Spectrewolf777/Stm32l4-Watch/Drivers/lvgl/lvgl/tests/ref_imgs/draw/render/al88/demo_render_image_normal_1_opa_128.png

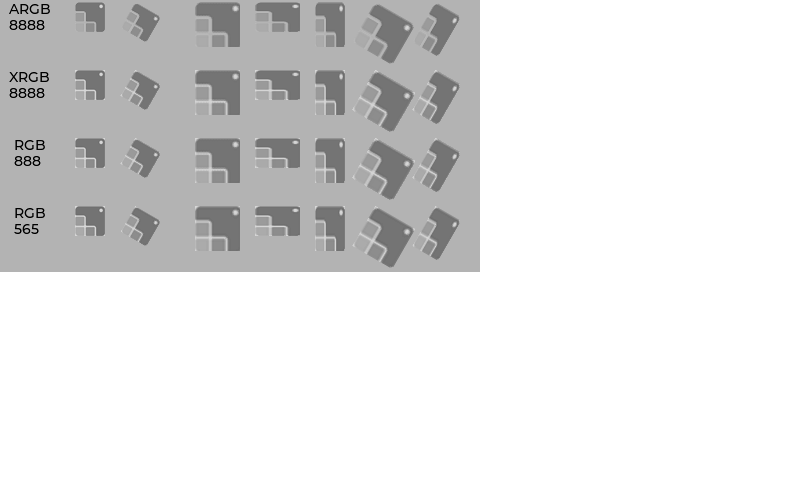
Drivers/lvgl/lvgl/tests/ref_imgs/draw/render/al88/demo_render_image_normal_1_opa_128.png
