Spectrewolf777/Stm32l4-Watch/Drivers/lvgl/lvgl/tests/ref_imgs/draw/render/argb8888/demo_render_arc_normal_opa_255.png

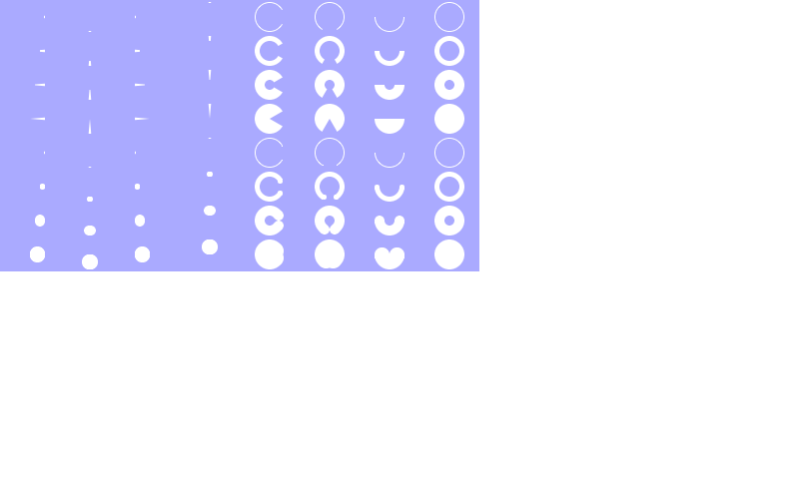
Drivers/lvgl/lvgl/tests/ref_imgs/draw/render/argb8888/demo_render_arc_normal_opa_255.png
