Spectrewolf777/Stm32l4-Watch/Drivers/lvgl/lvgl/tests/ref_imgs/draw/render/i1/demo_render_border_opa_192.png

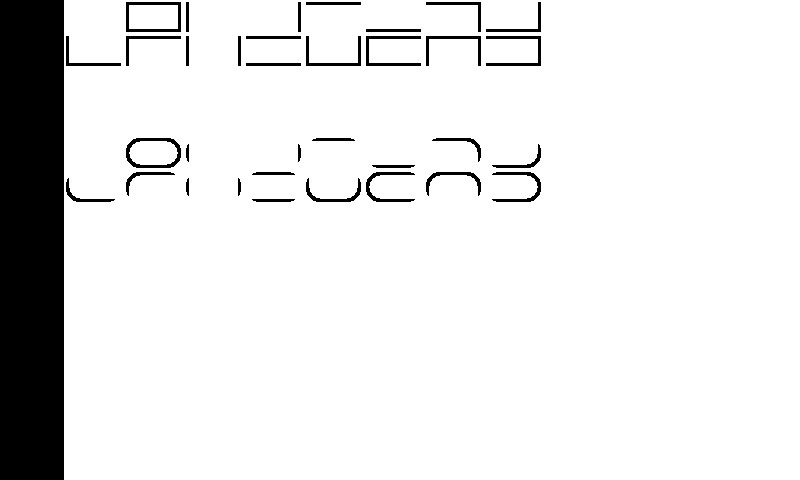
Drivers/lvgl/lvgl/tests/ref_imgs/draw/render/i1/demo_render_border_opa_192.png
