Spectrewolf777/Stm32l4-Watch/Drivers/lvgl/lvgl/tests/ref_imgs/draw/render/i1/demo_render_triangle_opa_255.png

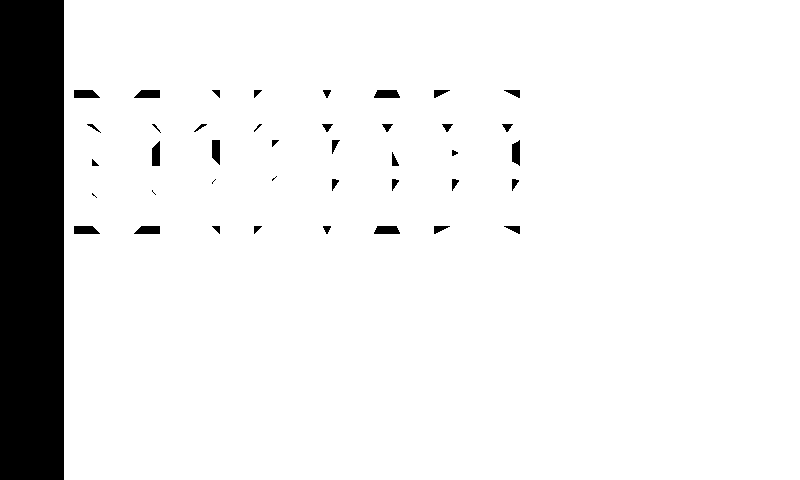
Drivers/lvgl/lvgl/tests/ref_imgs/draw/render/i1/demo_render_triangle_opa_255.png
