Spectrewolf777/Stm32l4-Watch/Drivers/lvgl/lvgl/tests/ref_imgs/draw/render/l8/demo_render_triangle_opa_128.png

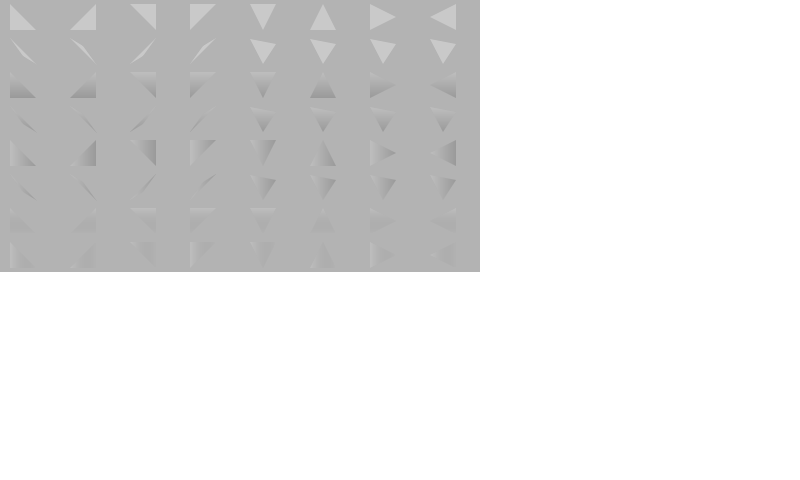
Drivers/lvgl/lvgl/tests/ref_imgs/draw/render/l8/demo_render_triangle_opa_128.png
