Spectrewolf777/Stm32l4-Watch/Drivers/lvgl/lvgl/tests/ref_imgs_vg_lite/draw/render/argb8888/demo_render_text_opa_128.png

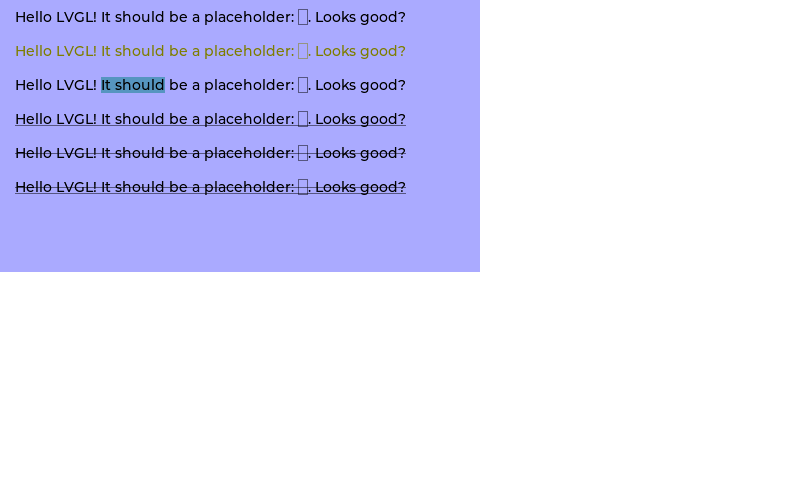
Drivers/lvgl/lvgl/tests/ref_imgs_vg_lite/draw/render/argb8888/demo_render_text_opa_128.png
