Spectrewolf777/Stm32l4-Watch/Core/Src/lsm6dsv16x_reg.c

/**
  ******************************************************************************
  * @file    lsm6dsv16x_reg.c
  * @author  Sensors Software Solution Team
  * @brief   LSM6DSV16X driver file
  ******************************************************************************
  * @attention
  *
  * Copyright (c) 2024 STMicroelectronics.
  * All rights reserved.
  *
  * This software is licensed under terms that can be found in the LICENSE file
  * in the root directory of this software component.
  * If no LICENSE file comes with this software, it is provided AS-IS.
  *
  ******************************************************************************
  */

#include <string.h>
#include "lsm6dsv16x_reg.h"

int32_t __weak lsm6dsv16x_read_reg(const stmdev_ctx_t *ctx, uint8_t reg,
                                   uint8_t *data,
                                   uint16_t len)
{
  int32_t ret = 0;

  if (ctx == NULL)
  {
    return -1;
  }

  ret = ctx->read_reg(ctx->handle, reg, data, len);

  return ret;
}

int32_t __weak lsm6dsv16x_write_reg(const stmdev_ctx_t *ctx, uint8_t reg,
                                    uint8_t *data,
                                    uint16_t len)
{
  int32_t ret = 0;

  if (ctx == NULL)
  {
    return -1;
  }

  ret = ctx->write_reg(ctx->handle, reg, data, len);

  return ret;
}

static void bytecpy(uint8_t *target, const uint8_t *source)
{
  if ((target != NULL) && (source != NULL))
  {
    *target = *source;
  }
}

float_t lsm6dsv16x_from_sflp_to_mg(int16_t lsb)
{
  return ((float_t)lsb) * 0.061f;
}

float_t lsm6dsv16x_from_fs2_to_mg(int16_t lsb)
{
  return ((float_t)lsb) * 0.061f;
}

float_t lsm6dsv16x_from_fs4_to_mg(int16_t lsb)
{
  return ((float_t)lsb) * 0.122f;
}

float_t lsm6dsv16x_from_fs8_to_mg(int16_t lsb)
{
  return ((float_t)lsb) * 0.244f;
}

float_t lsm6dsv16x_from_fs16_to_mg(int16_t lsb)
{
  return ((float_t)lsb) * 0.488f;
}

float_t lsm6dsv16x_from_fs125_to_mdps(int16_t lsb)
{
  return ((float_t)lsb) * 4.375f;
}

float_t lsm6dsv16x_from_fs250_to_mdps(int16_t lsb)
{
  return ((float_t)lsb) * 8.750f;
}

float_t lsm6dsv16x_from_fs500_to_mdps(int16_t lsb)
{
  return ((float_t)lsb) * 17.50f;
}

float_t lsm6dsv16x_from_fs1000_to_mdps(int16_t lsb)
{
  return ((float_t)lsb) * 35.0f;
}

float_t lsm6dsv16x_from_fs2000_to_mdps(int16_t lsb)
{
  return ((float_t)lsb) * 70.0f;
}

float_t lsm6dsv16x_from_fs4000_to_mdps(int16_t lsb)
{
  return ((float_t)lsb) * 140.0f;
}

float_t lsm6dsv16x_from_lsb_to_celsius(int16_t lsb)
{
  return (((float_t)lsb / 256.0f) + 25.0f);
}

float_t lsm6dsv16x_from_lsb_to_nsec(uint32_t lsb)
{
  return ((float_t)lsb * 21750.0f);
}

float_t lsm6dsv16x_from_lsb_to_mv(int16_t lsb)
{
  return ((float_t)lsb) / 78.0f;
}

/*
 * Original conversion routines taken from: https://github.com/numpy/numpy
 *
 * Converts from half-precision (16-bit) float number to single precision (32-bit).
 *
 * uint32_t  static uint32_t ToFloatBits(uint16_t h);
 * Released under BSD-3-Clause License
 */
static uint32_t ToFloatBits(uint16_t h)
{
  uint16_t h_exp = (h & 0x7c00u);
  uint32_t f_sgn = ((uint32_t)h & 0x8000u) << 16u;
  uint32_t result = {0};
  switch (h_exp)
  {
    case 0x0000u:   // 0 or subnormal
    {
      uint16_t h_sig = (h & 0x03ffu);
      // Signed zero
      if (h_sig == 0u)
      {
        result = f_sgn;
        break;
      }
      // Subnormal
      h_sig <<= 1u;
      while ((h_sig & 0x0400u) == 0u)
      {
        h_sig <<= 1u;
        h_exp++;
      }
      uint32_t f_exp = ((uint32_t)(127u - 15u - (uint32_t)h_exp)) << 23u;
      uint32_t f_sig = ((uint32_t)(h_sig & 0x03ffu)) << 13u;
      result = f_sgn + f_exp + f_sig;
      break;
    }
    case 0x7c00u: // inf or NaN
      // All-ones exponent and a copy of the significand
      result = f_sgn + 0x7f800000u + (((uint32_t)(h & 0x03ffu)) << 13u);
      break;
    default: // normalized
      // Just need to adjust the exponent and shift
      result = f_sgn + (((uint32_t)(h & 0x7fffu) + 0x1c000u) << 13u);
      break;
  }

  return result;
}

uint32_t lsm6dsv16x_from_f16_to_f32(uint16_t val)
{
  return ToFloatBits(val);
}


int32_t lsm6dsv16x_xl_offset_on_out_set(const stmdev_ctx_t *ctx, uint8_t val)
{
  lsm6dsv16x_ctrl9_t ctrl9 = {0};
  int32_t ret = 0;

  ret = lsm6dsv16x_read_reg(ctx, LSM6DSV16X_CTRL9, (uint8_t *)&ctrl9, 1);
  if (ret == 0)
  {
    ctrl9.usr_off_on_out = val;
    ret = lsm6dsv16x_write_reg(ctx, LSM6DSV16X_CTRL9, (uint8_t *)&ctrl9, 1);
  }

  return ret;
}

int32_t lsm6dsv16x_xl_offset_on_out_get(const stmdev_ctx_t *ctx, uint8_t *val)
{
  lsm6dsv16x_ctrl9_t ctrl9 = {0};
  int32_t ret = 0;

  ret = lsm6dsv16x_read_reg(ctx, LSM6DSV16X_CTRL9, (uint8_t *)&ctrl9, 1);
  if (ret != 0)
  {
    return ret;
  }

  *val = ctrl9.usr_off_on_out;

  return ret;
}

int32_t lsm6dsv16x_xl_offset_mg_set(const stmdev_ctx_t *ctx,
                                    lsm6dsv16x_xl_offset_mg_t val)
{
  lsm6dsv16x_z_ofs_usr_t z_ofs_usr = {0};
  lsm6dsv16x_y_ofs_usr_t y_ofs_usr = {0};
  lsm6dsv16x_x_ofs_usr_t x_ofs_usr = {0};
  lsm6dsv16x_ctrl9_t ctrl9 = {0};
  int32_t ret = 0;
  float_t tmp = 0;

  ret = lsm6dsv16x_read_reg(ctx, LSM6DSV16X_Z_OFS_USR, (uint8_t *)&z_ofs_usr, 1);
  ret += lsm6dsv16x_read_reg(ctx, LSM6DSV16X_Y_OFS_USR, (uint8_t *)&y_ofs_usr, 1);
  ret += lsm6dsv16x_read_reg(ctx, LSM6DSV16X_X_OFS_USR, (uint8_t *)&x_ofs_usr, 1);
  if (ret != 0)
  {
    return ret;
  }


  if ((val.x_mg < (0.0078125f * 127.0f)) && (val.x_mg > (0.0078125f * -127.0f)) &&
      (val.y_mg < (0.0078125f * 127.0f)) && (val.y_mg > (0.0078125f * -127.0f)) &&
      (val.z_mg < (0.0078125f * 127.0f)) && (val.z_mg > (0.0078125f * -127.0f)))
  {
    ctrl9.usr_off_w = 0;

    tmp = val.z_mg / 0.0078125f;
    z_ofs_usr.z_ofs_usr = (uint8_t)tmp;

    tmp = val.y_mg / 0.0078125f;
    y_ofs_usr.y_ofs_usr = (uint8_t)tmp;

    tmp = val.x_mg / 0.0078125f;
    x_ofs_usr.x_ofs_usr = (uint8_t)tmp;
  }
  else if ((val.x_mg < (0.125f * 127.0f)) && (val.x_mg > (0.125f * -127.0f)) &&
           (val.y_mg < (0.125f * 127.0f)) && (val.y_mg > (0.125f * -127.0f)) &&
           (val.z_mg < (0.125f * 127.0f)) && (val.z_mg > (0.125f * -127.0f)))
  {
    ctrl9.usr_off_w = 1;

    tmp = val.z_mg / 0.125f;
    z_ofs_usr.z_ofs_usr = (uint8_t)tmp;

    tmp = val.y_mg / 0.125f;
    y_ofs_usr.y_ofs_usr = (uint8_t)tmp;

    tmp = val.x_mg / 0.125f;
    x_ofs_usr.x_ofs_usr = (uint8_t)tmp;
  }
  else // out of limit
  {
    ctrl9.usr_off_w = 1;
    z_ofs_usr.z_ofs_usr = 0xFFU;
    y_ofs_usr.y_ofs_usr = 0xFFU;
    x_ofs_usr.x_ofs_usr = 0xFFU;
  }

  ret = lsm6dsv16x_write_reg(ctx, LSM6DSV16X_Z_OFS_USR, (uint8_t *)&z_ofs_usr, 1);
  ret += lsm6dsv16x_write_reg(ctx, LSM6DSV16X_Y_OFS_USR, (uint8_t *)&y_ofs_usr, 1);
  ret += lsm6dsv16x_write_reg(ctx, LSM6DSV16X_X_OFS_USR, (uint8_t *)&x_ofs_usr, 1);
  ret += lsm6dsv16x_write_reg(ctx, LSM6DSV16X_CTRL9, (uint8_t *)&ctrl9, 1);

  return ret;
}

int32_t lsm6dsv16x_xl_offset_mg_get(const stmdev_ctx_t *ctx,
                                    lsm6dsv16x_xl_offset_mg_t *val)
{
  lsm6dsv16x_z_ofs_usr_t z_ofs_usr = {0};
  lsm6dsv16x_y_ofs_usr_t y_ofs_usr = {0};
  lsm6dsv16x_x_ofs_usr_t x_ofs_usr = {0};
  lsm6dsv16x_ctrl9_t ctrl9 = {0};
  int32_t ret = 0;

  ret = lsm6dsv16x_read_reg(ctx, LSM6DSV16X_CTRL9, (uint8_t *)&ctrl9, 1);
  ret += lsm6dsv16x_read_reg(ctx, LSM6DSV16X_Z_OFS_USR, (uint8_t *)&z_ofs_usr, 1);
  ret += lsm6dsv16x_read_reg(ctx, LSM6DSV16X_Y_OFS_USR, (uint8_t *)&y_ofs_usr, 1);
  ret += lsm6dsv16x_read_reg(ctx, LSM6DSV16X_X_OFS_USR, (uint8_t *)&x_ofs_usr, 1);
  if (ret != 0)
  {
    return ret;
  }

  if (ctrl9.usr_off_w == PROPERTY_DISABLE)
  {
    val->z_mg = ((float_t)z_ofs_usr.z_ofs_usr * 0.0078125f);
    val->y_mg = ((float_t)y_ofs_usr.y_ofs_usr * 0.0078125f);
    val->x_mg = ((float_t)x_ofs_usr.x_ofs_usr * 0.0078125f);
  }
  else
  {
    val->z_mg = ((float_t)z_ofs_usr.z_ofs_usr * 0.125f);
    val->y_mg = ((float_t)y_ofs_usr.y_ofs_usr * 0.125f);
    val->x_mg = ((float_t)x_ofs_usr.x_ofs_usr * 0.125f);
  }

  return ret;
}

int32_t lsm6dsv16x_reboot(const stmdev_ctx_t *ctx)
{
  lsm6dsv16x_ctrl3_t ctrl3 = {0};
  lsm6dsv16x_data_rate_t data_rate_xl = {0};
  lsm6dsv16x_data_rate_t data_rate_gy = {0};
  int32_t ret = 0;

  if (ctx->mdelay == NULL)
  {
    ret = -1;
    goto exit;
  }

  ret = lsm6dsv16x_read_reg(ctx, LSM6DSV16X_CTRL3, (uint8_t *)&ctrl3, 1);
  if (ret != 0)
  {
    goto exit;
  }

  /* Save current data rates */
  ret = lsm6dsv16x_xl_data_rate_get(ctx, &data_rate_xl);
  ret += lsm6dsv16x_gy_data_rate_get(ctx, &data_rate_gy);
  if (ret != 0)
  {
    goto exit;
  }

  /* 1. Set the accelerometer and gyroscope in power-down mode */
  ret = lsm6dsv16x_xl_data_rate_set(ctx, LSM6DSV16X_ODR_OFF);
  ret += lsm6dsv16x_gy_data_rate_set(ctx, LSM6DSV16X_ODR_OFF);
  if (ret != 0)
  {
    goto exit;
  }

  /* 2. Set the BOOT bit of the CTRL3 register to 1. */
  ctrl3.boot = 1;
  ret = lsm6dsv16x_write_reg(ctx, LSM6DSV16X_CTRL3, (uint8_t *)&ctrl3, 1);
  if (ret != 0)
  {
    goto exit;
  }

  /* 3. Wait 30 ms. */
  ctx->mdelay(30);

  /* Restore data rates */
  ret = lsm6dsv16x_xl_data_rate_set(ctx, data_rate_xl);
  ret += lsm6dsv16x_gy_data_rate_set(ctx, data_rate_gy);

exit:
  return ret;
}

int32_t lsm6dsv16x_sw_por(const stmdev_ctx_t *ctx)
{
  lsm6dsv16x_func_cfg_access_t func_cfg_access = {0};
  int32_t ret = 0;

  if (ctx->mdelay == NULL)
  {
    ret = -1;
    goto exit;
  }

  /* 1. Set the SW_POR bit of the FUNC_CFG_ACCESS register to 1. */
  func_cfg_access.sw_por = 1;
  ret = lsm6dsv16x_write_reg(ctx, LSM6DSV16X_FUNC_CFG_ACCESS, (uint8_t *)&func_cfg_access, 1);
  if (ret != 0)
  {
    goto exit;
  }

  /* 2. Wait 30 ms. */
  ctx->mdelay(30);

exit:
  return ret;
}

int32_t lsm6dsv16x_sw_reset(const stmdev_ctx_t *ctx)
{
  lsm6dsv16x_ctrl3_t ctrl3 = {0};
  uint8_t retry = 0;
  int32_t ret = 0;

  if (ctx->mdelay == NULL)
  {
    ret = -1;
    goto exit;
  }

  /* 1. Set the accelerometer and gyroscope in power-down mode */
  ret = lsm6dsv16x_xl_data_rate_set(ctx, LSM6DSV16X_ODR_OFF);
  ret += lsm6dsv16x_gy_data_rate_set(ctx, LSM6DSV16X_ODR_OFF);
  if (ret != 0)
  {
    goto exit;
  }

  /* 2. Set the SW_RESET bit of the CTRL3 register to 1. */
  ctrl3.sw_reset = 1u;
  ret = lsm6dsv16x_write_reg(ctx, LSM6DSV16X_CTRL3, (uint8_t *)&ctrl3, 1);

  /* 3. Poll the SW_RESET bit of the CTRL3 register until it returns to 0. */
  do
  {
    ret += lsm6dsv16x_read_reg(ctx, LSM6DSV16X_CTRL3, (uint8_t *)&ctrl3, 1);
    if (ret != 0)
    {
      goto exit;
    }

    ctx->mdelay(1);
  } while (ctrl3.sw_reset == 1u && retry++ < 3u);

  return (ctrl3.sw_reset == 0u) ? 0 : -1;

exit:
  return ret;
}

int32_t lsm6dsv16x_mem_bank_set(const stmdev_ctx_t *ctx, lsm6dsv16x_mem_bank_t val)
{
  lsm6dsv16x_func_cfg_access_t func_cfg_access = {0};
  int32_t ret = 0;

  ret = lsm6dsv16x_read_reg(ctx, LSM6DSV16X_FUNC_CFG_ACCESS, (uint8_t *)&func_cfg_access, 1);
  if (ret != 0)
  {
    return ret;
  }

  func_cfg_access.shub_reg_access = ((uint8_t)val & 0x02U) >> 1;
  func_cfg_access.emb_func_reg_access = (uint8_t)val & 0x01U;
  ret = lsm6dsv16x_write_reg(ctx, LSM6DSV16X_FUNC_CFG_ACCESS, (uint8_t *)&func_cfg_access, 1);

  return ret;
}


int32_t lsm6dsv16x_mem_bank_get(const stmdev_ctx_t *ctx, lsm6dsv16x_mem_bank_t *val)
{
  lsm6dsv16x_func_cfg_access_t func_cfg_access = {0};
  int32_t ret = 0;

  ret = lsm6dsv16x_read_reg(ctx, LSM6DSV16X_FUNC_CFG_ACCESS, (uint8_t *)&func_cfg_access, 1);
  if (ret != 0)
  {
    return ret;
  }

  switch ((func_cfg_access.shub_reg_access << 1) + func_cfg_access.emb_func_reg_access)
  {
    case 0x00:
      *val = LSM6DSV16X_MAIN_MEM_BANK;
      break;

    case 0x01:
      *val = LSM6DSV16X_EMBED_FUNC_MEM_BANK;
      break;

    case 0x02:
      *val = LSM6DSV16X_SENSOR_HUB_MEM_BANK;
      break;

    default:
      *val = LSM6DSV16X_MAIN_MEM_BANK;
      break;
  }

  return ret;
}


int32_t lsm6dsv16x_device_id_get(const stmdev_ctx_t *ctx, uint8_t *val)
{
  int32_t ret = 0;

  ret = lsm6dsv16x_read_reg(ctx, LSM6DSV16X_WHO_AM_I, val, 1);

  return ret;
}

int32_t lsm6dsv16x_xl_data_rate_set(const stmdev_ctx_t *ctx,
                                    lsm6dsv16x_data_rate_t val)
{
  lsm6dsv16x_ctrl1_t ctrl1 = {0};
  lsm6dsv16x_haodr_cfg_t haodr = {0};
  uint8_t sel = 0;
  int32_t ret = 0;

  ret = lsm6dsv16x_read_reg(ctx, LSM6DSV16X_CTRL1, (uint8_t *)&ctrl1, 1);
  if (ret != 0)
  {
    return ret;
  }

  ctrl1.odr_xl = (uint8_t)val & 0x0Fu;
  ret = lsm6dsv16x_write_reg(ctx, LSM6DSV16X_CTRL1, (uint8_t *)&ctrl1, 1);
  if (ret != 0)
  {
    return ret;
  }

  sel = ((uint8_t)val >> 4) & 0xFU;
  if (sel != 0U)
  {
    ret += lsm6dsv16x_read_reg(ctx, LSM6DSV16X_HAODR_CFG, (uint8_t *)&haodr, 1);
    if (ret != 0)
    {
      return ret;
    }

    haodr.haodr_sel = sel;
    ret += lsm6dsv16x_write_reg(ctx, LSM6DSV16X_HAODR_CFG, (uint8_t *)&haodr, 1);
  }

  return ret;
}


int32_t lsm6dsv16x_xl_data_rate_get(const stmdev_ctx_t *ctx,
                                    lsm6dsv16x_data_rate_t *val)
{
  lsm6dsv16x_ctrl1_t ctrl1 = {0};
  lsm6dsv16x_haodr_cfg_t haodr = {0};
  uint8_t sel = 0;
  int32_t ret = 0;

  ret = lsm6dsv16x_read_reg(ctx, LSM6DSV16X_CTRL1, (uint8_t *)&ctrl1, 1);
  ret += lsm6dsv16x_read_reg(ctx, LSM6DSV16X_HAODR_CFG, (uint8_t *)&haodr, 1);
  if (ret != 0)
  {
    return ret;
  }

  sel = haodr.haodr_sel;

  switch (ctrl1.odr_xl)
  {
    case 0x00:
      *val = LSM6DSV16X_ODR_OFF;
      break;

    case 0x01:
      *val = LSM6DSV16X_ODR_AT_1Hz875;
      break;

    case 0x02:
      *val = LSM6DSV16X_ODR_AT_7Hz5;
      break;

    case 0x03:
      switch (sel)
      {
        default: /* sel == 0 or any unexpected value */
          *val = LSM6DSV16X_ODR_AT_15Hz;
          break;
        case 1:
          *val = LSM6DSV16X_ODR_HA01_AT_15Hz625;
          break;
        case 2:
          *val = LSM6DSV16X_ODR_HA02_AT_12Hz5;
          break;
      }
      break;

    case 0x04:
      switch (sel)
      {
        default: /* sel == 0 or any unexpected value */
          *val = LSM6DSV16X_ODR_AT_30Hz;
          break;
        case 1:
          *val = LSM6DSV16X_ODR_HA01_AT_31Hz25;
          break;
        case 2:
          *val = LSM6DSV16X_ODR_HA02_AT_25Hz;
          break;
      }
      break;

    case 0x05:
      switch (sel)
      {
        default: /* sel == 0 or any unexpected value */
          *val = LSM6DSV16X_ODR_AT_60Hz;
          break;
        case 1:
          *val = LSM6DSV16X_ODR_HA01_AT_62Hz5;
          break;
        case 2:
          *val = LSM6DSV16X_ODR_HA02_AT_50Hz;
          break;
      }
      break;

    case 0x06:
      switch (sel)
      {
        default: /* sel == 0 or any unexpected value */
          *val = LSM6DSV16X_ODR_AT_120Hz;
          break;
        case 1:
          *val = LSM6DSV16X_ODR_HA01_AT_125Hz;
          break;
        case 2:
          *val = LSM6DSV16X_ODR_HA02_AT_100Hz;
          break;
      }
      break;

    case 0x07:
      switch (sel)
      {
        default: /* sel == 0 or any unexpected value */
          *val = LSM6DSV16X_ODR_AT_240Hz;
          break;
        case 1:
          *val = LSM6DSV16X_ODR_HA01_AT_250Hz;
          break;
        case 2:
          *val = LSM6DSV16X_ODR_HA02_AT_200Hz;
          break;
      }
      break;

    case 0x08:
      switch (sel)
      {
        default: /* sel == 0 or any unexpected value */
          *val = LSM6DSV16X_ODR_AT_480Hz;
          break;
        case 1:
          *val = LSM6DSV16X_ODR_HA01_AT_500Hz;
          break;
        case 2:
          *val = LSM6DSV16X_ODR_HA02_AT_400Hz;
          break;
      }
      break;

    case 0x09:
      switch (sel)
      {
        default: /* sel == 0 or any unexpected value */
          *val = LSM6DSV16X_ODR_AT_960Hz;
          break;
        case 1:
          *val = LSM6DSV16X_ODR_HA01_AT_1000Hz;
          break;
        case 2:
          *val = LSM6DSV16X_ODR_HA02_AT_800Hz;
          break;
      }
      break;

    case 0x0A:
      switch (sel)
      {
        default: /* sel == 0 or any unexpected value */
          *val = LSM6DSV16X_ODR_AT_1920Hz;
          break;
        case 1:
          *val = LSM6DSV16X_ODR_HA01_AT_2000Hz;
          break;
        case 2:
          *val = LSM6DSV16X_ODR_HA02_AT_1600Hz;
          break;
      }
      break;

    case 0x0B:
      switch (sel)
      {
        default: /* sel == 0 or any unexpected value */
          *val = LSM6DSV16X_ODR_AT_3840Hz;
          break;
        case 1:
          *val = LSM6DSV16X_ODR_HA01_AT_4000Hz;
          break;
        case 2:
          *val = LSM6DSV16X_ODR_HA02_AT_3200Hz;
          break;
      }
      break;

    case 0x0C:
      switch (sel)
      {
        default: /* sel == 0 or any unexpected value */
          *val = LSM6DSV16X_ODR_AT_7680Hz;
          break;
        case 1:
          *val = LSM6DSV16X_ODR_HA01_AT_8000Hz;
          break;
        case 2:
          *val = LSM6DSV16X_ODR_HA02_AT_6400Hz;
          break;
      }
      break;

    default:
      *val = LSM6DSV16X_ODR_OFF;
      break;
  }

  return ret;
}


int32_t lsm6dsv16x_xl_mode_set(const stmdev_ctx_t *ctx, lsm6dsv16x_xl_mode_t val)
{
  lsm6dsv16x_ctrl1_t ctrl1 = {0};
  int32_t ret = 0;

  ret = lsm6dsv16x_read_reg(ctx, LSM6DSV16X_CTRL1, (uint8_t *)&ctrl1, 1);

  if (ret == 0)
  {
    ctrl1.op_mode_xl = (uint8_t)val & 0x07U;
    ret = lsm6dsv16x_write_reg(ctx, LSM6DSV16X_CTRL1, (uint8_t *)&ctrl1, 1);
  }

  return ret;
}

int32_t lsm6dsv16x_xl_mode_get(const stmdev_ctx_t *ctx, lsm6dsv16x_xl_mode_t *val)
{
  lsm6dsv16x_ctrl1_t ctrl1 = {0};
  int32_t ret = 0;

  ret = lsm6dsv16x_read_reg(ctx, LSM6DSV16X_CTRL1, (uint8_t *)&ctrl1, 1);
  if (ret != 0)
  {
    return ret;
  }

  switch (ctrl1.op_mode_xl)
  {
    case 0x00:
      *val = LSM6DSV16X_XL_HIGH_PERFORMANCE_MD;
      break;

    case 0x01:
      *val = LSM6DSV16X_XL_HIGH_ACCURACY_ODR_MD;
      break;

    case 0x03:
      *val = LSM6DSV16X_XL_ODR_TRIGGERED_MD;
      break;

    case 0x04:
      *val = LSM6DSV16X_XL_LOW_POWER_2_AVG_MD;
      break;

    case 0x05:
      *val = LSM6DSV16X_XL_LOW_POWER_4_AVG_MD;
      break;

    case 0x06:
      *val = LSM6DSV16X_XL_LOW_POWER_8_AVG_MD;
      break;

    case 0x07:
      *val = LSM6DSV16X_XL_NORMAL_MD;
      break;

    default:
      *val = LSM6DSV16X_XL_HIGH_PERFORMANCE_MD;
      break;
  }

  return ret;
}


int32_t lsm6dsv16x_gy_data_rate_set(const stmdev_ctx_t *ctx,
                                    lsm6dsv16x_data_rate_t val)
{
  lsm6dsv16x_ctrl2_t ctrl2 = {0};
  lsm6dsv16x_haodr_cfg_t haodr = {0};
  uint8_t sel = 0;
  int32_t ret = 0;

  ret = lsm6dsv16x_read_reg(ctx, LSM6DSV16X_CTRL2, (uint8_t *)&ctrl2, 1);
  if (ret != 0)
  {
    return ret;
  }

  ctrl2.odr_g = (uint8_t)val & 0x0Fu;
  ret += lsm6dsv16x_write_reg(ctx, LSM6DSV16X_CTRL2, (uint8_t *)&ctrl2, 1);
  if (ret != 0)
  {
    return ret;
  }

  sel = ((uint8_t)val >> 4) & 0xFU;
  if (sel != 0U)
  {
    ret += lsm6dsv16x_read_reg(ctx, LSM6DSV16X_HAODR_CFG, (uint8_t *)&haodr, 1);
    if (ret != 0)
    {
      return ret;
    }

    haodr.haodr_sel = sel;
    ret += lsm6dsv16x_write_reg(ctx, LSM6DSV16X_HAODR_CFG, (uint8_t *)&haodr, 1);
  }

  return ret;
}


int32_t lsm6dsv16x_gy_data_rate_get(const stmdev_ctx_t *ctx,
                                    lsm6dsv16x_data_rate_t *val)
{
  lsm6dsv16x_ctrl2_t ctrl2 = {0};
  lsm6dsv16x_haodr_cfg_t haodr = {0};
  uint8_t sel = 0;
  int32_t ret = 0;

  ret = lsm6dsv16x_read_reg(ctx, LSM6DSV16X_CTRL2, (uint8_t *)&ctrl2, 1);
  ret += lsm6dsv16x_read_reg(ctx, LSM6DSV16X_HAODR_CFG, (uint8_t *)&haodr, 1);
  if (ret != 0)
  {
    return ret;
  }

  sel = haodr.haodr_sel;

  switch (ctrl2.odr_g)
  {
    case 0x00:
      *val = LSM6DSV16X_ODR_OFF;
      break;

    case 0x01:
      *val = LSM6DSV16X_ODR_AT_1Hz875;
      break;

    case 0x02:
      *val = LSM6DSV16X_ODR_AT_7Hz5;
      break;

    case 0x03:
      switch (sel)
      {
        default: /* sel == 0 or any unexpected value */
          *val = LSM6DSV16X_ODR_AT_15Hz;
          break;
        case 1:
          *val = LSM6DSV16X_ODR_HA01_AT_15Hz625;
          break;
        case 2:
          *val = LSM6DSV16X_ODR_HA02_AT_12Hz5;
          break;
      }
      break;

    case 0x04:
      switch (sel)
      {
        default: /* sel == 0 or any unexpected value */
          *val = LSM6DSV16X_ODR_AT_30Hz;
          break;
        case 1:
          *val = LSM6DSV16X_ODR_HA01_AT_31Hz25;
          break;
        case 2:
          *val = LSM6DSV16X_ODR_HA02_AT_25Hz;
          break;
      }
      break;

    case 0x05:
      switch (sel)
      {
        default: /* sel == 0 or any unexpected value */
          *val = LSM6DSV16X_ODR_AT_60Hz;
          break;
        case 1:
          *val = LSM6DSV16X_ODR_HA01_AT_62Hz5;
          break;
        case 2:
          *val = LSM6DSV16X_ODR_HA02_AT_50Hz;
          break;
      }
      break;

    case 0x06:
      switch (sel)
      {
        default: /* sel == 0 or any unexpected value */
          *val = LSM6DSV16X_ODR_AT_120Hz;
          break;
        case 1:
          *val = LSM6DSV16X_ODR_HA01_AT_125Hz;
          break;
        case 2:
          *val = LSM6DSV16X_ODR_HA02_AT_100Hz;
          break;
      }
      break;

    case 0x07:
      switch (sel)
      {
        default: /* sel == 0 or any unexpected value */
          *val = LSM6DSV16X_ODR_AT_240Hz;
          break;
        case 1:
          *val = LSM6DSV16X_ODR_HA01_AT_250Hz;
          break;
        case 2:
          *val = LSM6DSV16X_ODR_HA02_AT_200Hz;
          break;
      }
      break;

    case 0x08:
      switch (sel)
      {
        default: /* sel == 0 or any unexpected value */
          *val = LSM6DSV16X_ODR_AT_480Hz;
          break;
        case 1:
          *val = LSM6DSV16X_ODR_HA01_AT_500Hz;
          break;
        case 2:
          *val = LSM6DSV16X_ODR_HA02_AT_400Hz;
          break;
      }
      break;

    case 0x09:
      switch (sel)
      {
        default: /* sel == 0 or any unexpected value */
          *val = LSM6DSV16X_ODR_AT_960Hz;
          break;
        case 1:
          *val = LSM6DSV16X_ODR_HA01_AT_1000Hz;
          break;
        case 2:
          *val = LSM6DSV16X_ODR_HA02_AT_800Hz;
          break;
      }
      break;

    case 0x0A:
      switch (sel)
      {
        default: /* sel == 0 or any unexpected value */
          *val = LSM6DSV16X_ODR_AT_1920Hz;
          break;
        case 1:
          *val = LSM6DSV16X_ODR_HA01_AT_2000Hz;
          break;
        case 2:
          *val = LSM6DSV16X_ODR_HA02_AT_1600Hz;
          break;
      }
      break;

    case 0x0B:
      switch (sel)
      {
        default: /* sel == 0 or any unexpected value */
          *val = LSM6DSV16X_ODR_AT_3840Hz;
          break;
        case 1:
          *val = LSM6DSV16X_ODR_HA01_AT_4000Hz;
          break;
        case 2:
          *val = LSM6DSV16X_ODR_HA02_AT_3200Hz;
          break;
      }
      break;

    case 0x0C:
      switch (sel)
      {
        default: /* sel == 0 or any unexpected value */
          *val = LSM6DSV16X_ODR_AT_7680Hz;
          break;
        case 1:
          *val = LSM6DSV16X_ODR_HA01_AT_8000Hz;
          break;
        case 2:
          *val = LSM6DSV16X_ODR_HA02_AT_6400Hz;
          break;
      }
      break;

    default:
      *val = LSM6DSV16X_ODR_OFF;
      break;
  }

  return ret;
}


int32_t lsm6dsv16x_gy_mode_set(const stmdev_ctx_t *ctx, lsm6dsv16x_gy_mode_t val)
{
  lsm6dsv16x_ctrl2_t ctrl2 = {0};
  int32_t ret = 0;

  ret = lsm6dsv16x_read_reg(ctx, LSM6DSV16X_CTRL2, (uint8_t *)&ctrl2, 1);
  if (ret == 0)
  {
    ctrl2.op_mode_g = (uint8_t)val & 0x07U;
    ret = lsm6dsv16x_write_reg(ctx, LSM6DSV16X_CTRL2, (uint8_t *)&ctrl2, 1);
  }

  return ret;
}


int32_t lsm6dsv16x_gy_mode_get(const stmdev_ctx_t *ctx, lsm6dsv16x_gy_mode_t *val)
{
  lsm6dsv16x_ctrl2_t ctrl2 = {0};
  int32_t ret = 0;

  ret = lsm6dsv16x_read_reg(ctx, LSM6DSV16X_CTRL2, (uint8_t *)&ctrl2, 1);
  if (ret != 0)
  {
    return ret;
  }

  switch (ctrl2.op_mode_g)
  {
    case 0x00:
      *val = LSM6DSV16X_GY_HIGH_PERFORMANCE_MD;
      break;

    case 0x01:
      *val = LSM6DSV16X_GY_HIGH_ACCURACY_ODR_MD;
      break;

    case 0x04:
      *val = LSM6DSV16X_GY_SLEEP_MD;
      break;

    case 0x05:
      *val = LSM6DSV16X_GY_LOW_POWER_MD;
      break;

    default:
      *val = LSM6DSV16X_GY_HIGH_PERFORMANCE_MD;
      break;
  }

  return ret;
}


int32_t lsm6dsv16x_auto_increment_set(const stmdev_ctx_t *ctx, uint8_t val)
{
  lsm6dsv16x_ctrl3_t ctrl3 = {0};
  int32_t ret = 0;

  ret = lsm6dsv16x_read_reg(ctx, LSM6DSV16X_CTRL3, (uint8_t *)&ctrl3, 1);
  if (ret == 0)
  {
    ctrl3.if_inc = val;
    ret = lsm6dsv16x_write_reg(ctx, LSM6DSV16X_CTRL3, (uint8_t *)&ctrl3, 1);
  }

  return ret;
}

int32_t lsm6dsv16x_auto_increment_get(const stmdev_ctx_t *ctx, uint8_t *val)
{
  lsm6dsv16x_ctrl3_t ctrl3 = {0};
  int32_t ret = 0;

  ret = lsm6dsv16x_read_reg(ctx, LSM6DSV16X_CTRL3, (uint8_t *)&ctrl3, 1);
  if (ret != 0)
  {
    return ret;
  }

  *val = ctrl3.if_inc;

  return ret;
}


int32_t lsm6dsv16x_block_data_update_set(const stmdev_ctx_t *ctx, uint8_t val)
{
  lsm6dsv16x_ctrl3_t ctrl3 = {0};
  int32_t ret = 0;

  ret = lsm6dsv16x_read_reg(ctx, LSM6DSV16X_CTRL3, (uint8_t *)&ctrl3, 1);

  if (ret == 0)
  {
    ctrl3.bdu = val;
    ret = lsm6dsv16x_write_reg(ctx, LSM6DSV16X_CTRL3, (uint8_t *)&ctrl3, 1);
  }

  return ret;
}

int32_t lsm6dsv16x_block_data_update_get(const stmdev_ctx_t *ctx, uint8_t *val)
{
  lsm6dsv16x_ctrl3_t ctrl3 = {0};
  int32_t ret = 0;

  ret = lsm6dsv16x_read_reg(ctx, LSM6DSV16X_CTRL3, (uint8_t *)&ctrl3, 1);
  if (ret != 0)
  {
    return ret;
  }

  *val = ctrl3.bdu;

  return ret;
}


int32_t lsm6dsv16x_odr_trig_cfg_set(const stmdev_ctx_t *ctx, uint8_t val)
{
  lsm6dsv16x_odr_trig_cfg_t odr_trig = {0};
  int32_t ret = 0;

  if (val >= 1U && val <= 3U)
  {
    return -1;
  }

  ret = lsm6dsv16x_read_reg(ctx, LSM6DSV16X_ODR_TRIG_CFG, (uint8_t *)&odr_trig, 1);

  if (ret == 0)
  {
    odr_trig.odr_trig_nodr = val;
    ret = lsm6dsv16x_write_reg(ctx, LSM6DSV16X_ODR_TRIG_CFG, (uint8_t *)&odr_trig, 1);
  }

  return ret;
}


int32_t lsm6dsv16x_odr_trig_cfg_get(const stmdev_ctx_t *ctx, uint8_t *val)
{
  lsm6dsv16x_odr_trig_cfg_t odr_trig = {0};
  int32_t ret = 0;

  ret = lsm6dsv16x_read_reg(ctx, LSM6DSV16X_ODR_TRIG_CFG, (uint8_t *)&odr_trig, 1);
  if (ret != 0)
  {
    return ret;
  }

  *val = odr_trig.odr_trig_nodr;

  return ret;
}


int32_t lsm6dsv16x_data_ready_mode_set(const stmdev_ctx_t *ctx,
                                       lsm6dsv16x_data_ready_mode_t val)
{
  lsm6dsv16x_ctrl4_t ctrl4 = {0};
  int32_t ret = 0;

  ret = lsm6dsv16x_read_reg(ctx, LSM6DSV16X_CTRL4, (uint8_t *)&ctrl4, 1);

  if (ret == 0)
  {
    ctrl4.drdy_pulsed = (uint8_t)val & 0x1U;
    ret = lsm6dsv16x_write_reg(ctx, LSM6DSV16X_CTRL4, (uint8_t *)&ctrl4, 1);
  }

  return ret;
}


int32_t lsm6dsv16x_data_ready_mode_get(const stmdev_ctx_t *ctx,
                                       lsm6dsv16x_data_ready_mode_t *val)
{
  lsm6dsv16x_ctrl4_t ctrl4 = {0};
  int32_t ret = 0;

  ret = lsm6dsv16x_read_reg(ctx, LSM6DSV16X_CTRL4, (uint8_t *)&ctrl4, 1);
  if (ret != 0)
  {
    return ret;
  }

  switch (ctrl4.drdy_pulsed)
  {
    case 0x00:
      *val = LSM6DSV16X_DRDY_LATCHED;
      break;

    case 0x01:
      *val = LSM6DSV16X_DRDY_PULSED;
      break;

    default:
      *val = LSM6DSV16X_DRDY_LATCHED;
      break;
  }

  return ret;
}


int32_t lsm6dsv16x_interrupt_enable_set(const stmdev_ctx_t *ctx,
                                        lsm6dsv16x_interrupt_mode_t val)
{
  lsm6dsv16x_tap_cfg0_t cfg = {0};
  lsm6dsv16x_functions_enable_t func = {0};
  int32_t ret = 0;

  ret = lsm6dsv16x_read_reg(ctx, LSM6DSV16X_FUNCTIONS_ENABLE, (uint8_t *)&func, 1);
  if (ret != 0)
  {
    return ret;
  }
  func.interrupts_enable = val.enable;
  ret = lsm6dsv16x_write_reg(ctx, LSM6DSV16X_FUNCTIONS_ENABLE, (uint8_t *)&func, 1);

  ret += lsm6dsv16x_read_reg(ctx, LSM6DSV16X_TAP_CFG0, (uint8_t *)&cfg, 1);
  if (ret != 0)
  {
    return ret;
  }
  cfg.lir = val.lir;
  ret += lsm6dsv16x_write_reg(ctx, LSM6DSV16X_TAP_CFG0, (uint8_t *)&cfg, 1);

  return ret;
}


int32_t lsm6dsv16x_interrupt_enable_get(const stmdev_ctx_t *ctx,
                                        lsm6dsv16x_interrupt_mode_t *val)
{
  lsm6dsv16x_tap_cfg0_t cfg = {0};
  lsm6dsv16x_functions_enable_t func = {0};
  int32_t ret = 0;

  ret = lsm6dsv16x_read_reg(ctx, LSM6DSV16X_FUNCTIONS_ENABLE, (uint8_t *)&func, 1);
  ret += lsm6dsv16x_read_reg(ctx, LSM6DSV16X_TAP_CFG0, (uint8_t *)&cfg, 1);
  if (ret != 0)
  {
    return ret;
  }

  val->enable = func.interrupts_enable;
  val->lir = cfg.lir;

  return ret;
}


int32_t lsm6dsv16x_gy_full_scale_set(const stmdev_ctx_t *ctx,
                                     lsm6dsv16x_gy_full_scale_t val)
{
  lsm6dsv16x_ctrl6_t ctrl6 = {0};
  int32_t ret = 0;

  ret = lsm6dsv16x_read_reg(ctx, LSM6DSV16X_CTRL6, (uint8_t *)&ctrl6, 1);

  if (ret == 0)
  {
    ctrl6.fs_g = (uint8_t)val & 0xfu;
    ret = lsm6dsv16x_write_reg(ctx, LSM6DSV16X_CTRL6, (uint8_t *)&ctrl6, 1);
  }

  return ret;
}


int32_t lsm6dsv16x_gy_full_scale_get(const stmdev_ctx_t *ctx,
                                     lsm6dsv16x_gy_full_scale_t *val)
{
  lsm6dsv16x_ctrl6_t ctrl6 = {0};
  int32_t ret = 0;

  ret = lsm6dsv16x_read_reg(ctx, LSM6DSV16X_CTRL6, (uint8_t *)&ctrl6, 1);
  if (ret != 0)
  {
    return ret;
  }

  switch (ctrl6.fs_g)
  {
    case 0x00:
      *val = LSM6DSV16X_125dps;
      break;

    case 0x01:
      *val = LSM6DSV16X_250dps;
      break;

    case 0x02:
      *val = LSM6DSV16X_500dps;
      break;

    case 0x03:
      *val = LSM6DSV16X_1000dps;
      break;

    case 0x04:
      *val = LSM6DSV16X_2000dps;
      break;

    case 0x0C:
      *val = LSM6DSV16X_4000dps;
      break;

    default:
      *val = LSM6DSV16X_125dps;
      break;
  }

  return ret;
}


int32_t lsm6dsv16x_xl_full_scale_set(const stmdev_ctx_t *ctx,
                                     lsm6dsv16x_xl_full_scale_t val)
{
  lsm6dsv16x_ctrl8_t ctrl8 = {0};
  int32_t ret = 0;

  ret = lsm6dsv16x_read_reg(ctx, LSM6DSV16X_CTRL8, (uint8_t *)&ctrl8, 1);

  if (ret == 0)
  {
    ctrl8.fs_xl = (uint8_t)val & 0x3U;
    ret = lsm6dsv16x_write_reg(ctx, LSM6DSV16X_CTRL8, (uint8_t *)&ctrl8, 1);
  }

  return ret;
}


int32_t lsm6dsv16x_xl_full_scale_get(const stmdev_ctx_t *ctx,
                                     lsm6dsv16x_xl_full_scale_t *val)
{
  lsm6dsv16x_ctrl8_t ctrl8 = {0};
  int32_t ret = 0;

  ret = lsm6dsv16x_read_reg(ctx, LSM6DSV16X_CTRL8, (uint8_t *)&ctrl8, 1);
  if (ret != 0)
  {
    return ret;
  }

  switch (ctrl8.fs_xl)
  {
    case 0x00:
      *val = LSM6DSV16X_2g;
      break;

    case 0x01:
      *val = LSM6DSV16X_4g;
      break;

    case 0x02:
      *val = LSM6DSV16X_8g;
      break;

    case 0x03:
      *val = LSM6DSV16X_16g;
      break;

    default:
      *val = LSM6DSV16X_2g;
      break;
  }

  return ret;
}


int32_t lsm6dsv16x_xl_dual_channel_set(const stmdev_ctx_t *ctx, uint8_t val)
{
  lsm6dsv16x_ctrl8_t ctrl8 = {0};
  int32_t ret = 0;

  ret = lsm6dsv16x_read_reg(ctx, LSM6DSV16X_CTRL8, (uint8_t *)&ctrl8, 1);

  if (ret == 0)
  {
    ctrl8.xl_dualc_en = val;
    ret = lsm6dsv16x_write_reg(ctx, LSM6DSV16X_CTRL8, (uint8_t *)&ctrl8, 1);
  }

  return ret;
}

int32_t lsm6dsv16x_xl_dual_channel_get(const stmdev_ctx_t *ctx, uint8_t *val)
{
  lsm6dsv16x_ctrl8_t ctrl8 = {0};
  int32_t ret = 0;

  ret = lsm6dsv16x_read_reg(ctx, LSM6DSV16X_CTRL8, (uint8_t *)&ctrl8, 1);
  if (ret != 0)
  {
    return ret;
  }

  *val = ctrl8.xl_dualc_en;

  return ret;
}


int32_t lsm6dsv16x_xl_self_test_set(const stmdev_ctx_t *ctx,
                                    lsm6dsv16x_xl_self_test_t val)
{
  lsm6dsv16x_ctrl10_t ctrl10 = {0};
  int32_t ret = 0;

  ret = lsm6dsv16x_read_reg(ctx, LSM6DSV16X_CTRL10, (uint8_t *)&ctrl10, 1);

  if (ret == 0)
  {
    ctrl10.st_xl = (uint8_t)val & 0x3U;
    ret = lsm6dsv16x_write_reg(ctx, LSM6DSV16X_CTRL10, (uint8_t *)&ctrl10, 1);
  }

  return ret;
}


int32_t lsm6dsv16x_xl_self_test_get(const stmdev_ctx_t *ctx,
                                    lsm6dsv16x_xl_self_test_t *val)
{
  lsm6dsv16x_ctrl10_t ctrl10 = {0};
  int32_t ret = 0;

  ret = lsm6dsv16x_read_reg(ctx, LSM6DSV16X_CTRL10, (uint8_t *)&ctrl10, 1);
  if (ret != 0)
  {
    return ret;
  }

  switch (ctrl10.st_xl)
  {
    case 0x00:
      *val = LSM6DSV16X_XL_ST_DISABLE;
      break;

    case 0x01:
      *val = LSM6DSV16X_XL_ST_POSITIVE;
      break;

    case 0x02:
      *val = LSM6DSV16X_XL_ST_NEGATIVE;
      break;

    default:
      *val = LSM6DSV16X_XL_ST_DISABLE;
      break;
  }

  return ret;
}


int32_t lsm6dsv16x_gy_self_test_set(const stmdev_ctx_t *ctx,
                                    lsm6dsv16x_gy_self_test_t val)
{
  lsm6dsv16x_ctrl10_t ctrl10 = {0};
  int32_t ret = 0;

  ret = lsm6dsv16x_read_reg(ctx, LSM6DSV16X_CTRL10, (uint8_t *)&ctrl10, 1);

  if (ret == 0)
  {
    ctrl10.st_g = (uint8_t)val & 0x3U;
    ret = lsm6dsv16x_write_reg(ctx, LSM6DSV16X_CTRL10, (uint8_t *)&ctrl10, 1);
  }

  return ret;
}


int32_t lsm6dsv16x_gy_self_test_get(const stmdev_ctx_t *ctx,
                                    lsm6dsv16x_gy_self_test_t *val)
{
  lsm6dsv16x_ctrl10_t ctrl10 = {0};
  int32_t ret = 0;

  ret = lsm6dsv16x_read_reg(ctx, LSM6DSV16X_CTRL10, (uint8_t *)&ctrl10, 1);
  if (ret != 0)
  {
    return ret;
  }

  switch (ctrl10.st_g)
  {
    case 0x00:
      *val = LSM6DSV16X_GY_ST_DISABLE;
      break;

    case 0x01:
      *val = LSM6DSV16X_GY_ST_POSITIVE;
      break;

    case 0x02:
      *val = LSM6DSV16X_GY_ST_NEGATIVE;
      break;

    default:
      *val = LSM6DSV16X_GY_ST_DISABLE;
      break;
  }

  return ret;
}


int32_t lsm6dsv16x_ois_xl_self_test_set(const stmdev_ctx_t *ctx,
                                        lsm6dsv16x_ois_xl_self_test_t val)
{
  lsm6dsv16x_spi2_int_ois_t spi2_int_ois = {0};
  int32_t ret = 0;

  ret = lsm6dsv16x_read_reg(ctx, LSM6DSV16X_SPI2_INT_OIS, (uint8_t *)&spi2_int_ois, 1);

  if (ret == 0)
  {
    spi2_int_ois.st_xl_ois = ((uint8_t)val & 0x3U);
    ret = lsm6dsv16x_write_reg(ctx, LSM6DSV16X_SPI2_INT_OIS, (uint8_t *)&spi2_int_ois, 1);
  }

  return ret;
}


int32_t lsm6dsv16x_ois_xl_self_test_get(const stmdev_ctx_t *ctx,
                                        lsm6dsv16x_ois_xl_self_test_t *val)
{
  lsm6dsv16x_spi2_int_ois_t spi2_int_ois = {0};
  int32_t ret = 0;

  ret = lsm6dsv16x_read_reg(ctx, LSM6DSV16X_SPI2_INT_OIS, (uint8_t *)&spi2_int_ois, 1);
  if (ret != 0)
  {
    return ret;
  }

  switch (spi2_int_ois.st_xl_ois)
  {
    case 0x00:
      *val = LSM6DSV16X_OIS_XL_ST_DISABLE;
      break;

    case 0x01:
      *val = LSM6DSV16X_OIS_XL_ST_POSITIVE;
      break;

    case 0x02:
      *val = LSM6DSV16X_OIS_XL_ST_NEGATIVE;
      break;

    default:
      *val = LSM6DSV16X_OIS_XL_ST_DISABLE;
      break;
  }

  return ret;
}


int32_t lsm6dsv16x_ois_gy_self_test_set(const stmdev_ctx_t *ctx,
                                        lsm6dsv16x_ois_gy_self_test_t val)
{
  lsm6dsv16x_spi2_int_ois_t spi2_int_ois = {0};
  int32_t ret = 0;

  ret = lsm6dsv16x_read_reg(ctx, LSM6DSV16X_SPI2_INT_OIS, (uint8_t *)&spi2_int_ois, 1);

  if (ret == 0)
  {
    spi2_int_ois.st_g_ois = ((uint8_t)val & 0x3U);
    spi2_int_ois.st_ois_clampdis = ((uint8_t)val & 0x04U) >> 2;
    ret = lsm6dsv16x_write_reg(ctx, LSM6DSV16X_SPI2_INT_OIS, (uint8_t *)&spi2_int_ois, 1);
  }

  return ret;
}


int32_t lsm6dsv16x_ois_gy_self_test_get(const stmdev_ctx_t *ctx,
                                        lsm6dsv16x_ois_gy_self_test_t *val)
{
  lsm6dsv16x_spi2_int_ois_t spi2_int_ois = {0};
  int32_t ret = 0;

  ret = lsm6dsv16x_read_reg(ctx, LSM6DSV16X_SPI2_INT_OIS, (uint8_t *)&spi2_int_ois, 1);
  if (ret != 0)
  {
    return ret;
  }

  switch (spi2_int_ois.st_g_ois)
  {
    case 0x00:
      *val = LSM6DSV16X_OIS_GY_ST_DISABLE;
      break;

    case 0x01:
      *val = (spi2_int_ois.st_ois_clampdis == 1U) ? LSM6DSV16X_OIS_GY_ST_CLAMP_POS :
             LSM6DSV16X_OIS_GY_ST_POSITIVE;
      break;

    case 0x02:
      *val = (spi2_int_ois.st_ois_clampdis == 1U) ? LSM6DSV16X_OIS_GY_ST_CLAMP_NEG :
             LSM6DSV16X_OIS_GY_ST_NEGATIVE;
      break;

    default:
      *val = LSM6DSV16X_OIS_GY_ST_DISABLE;
      break;
  }

  return ret;
}

int32_t lsm6dsv16x_pin_int1_route_set(const stmdev_ctx_t *ctx,
                                      lsm6dsv16x_pin_int_route_t *val)
{
  lsm6dsv16x_int1_ctrl_t          int1_ctrl = {0};
  lsm6dsv16x_md1_cfg_t            md1_cfg = {0};
  int32_t                    ret = 0;

  ret = lsm6dsv16x_read_reg(ctx, LSM6DSV16X_INT1_CTRL, (uint8_t *)&int1_ctrl, 1);
  if (ret != 0)
  {
    return ret;
  }

  int1_ctrl.int1_drdy_xl       = val->drdy_xl;
  int1_ctrl.int1_drdy_g        = val->drdy_g;
  int1_ctrl.int1_fifo_th       = val->fifo_th;
  int1_ctrl.int1_fifo_ovr      = val->fifo_ovr;
  int1_ctrl.int1_fifo_full     = val->fifo_full;
  int1_ctrl.int1_cnt_bdr       = val->cnt_bdr;

  ret = lsm6dsv16x_write_reg(ctx, LSM6DSV16X_INT1_CTRL, (uint8_t *)&int1_ctrl, 1);

  ret += lsm6dsv16x_read_reg(ctx, LSM6DSV16X_MD1_CFG, (uint8_t *)&md1_cfg, 1);
  if (ret != 0)
  {
    return ret;
  }

  md1_cfg.int1_shub            = val->shub;
  md1_cfg.int1_emb_func        = val->emb_func;
  md1_cfg.int1_6d              = val->sixd;
  md1_cfg.int1_single_tap      = val->single_tap;
  md1_cfg.int1_double_tap      = val->double_tap;
  md1_cfg.int1_wu              = val->wakeup;
  md1_cfg.int1_ff              = val->freefall;
  md1_cfg.int1_sleep_change    = val->sleep_change;

  ret = lsm6dsv16x_write_reg(ctx, LSM6DSV16X_MD1_CFG, (uint8_t *)&md1_cfg, 1);

  return ret;
}


int32_t lsm6dsv16x_pin_int1_route_get(const stmdev_ctx_t *ctx,
                                      lsm6dsv16x_pin_int_route_t *val)
{
  lsm6dsv16x_int1_ctrl_t          int1_ctrl = {0};
  lsm6dsv16x_md1_cfg_t            md1_cfg = {0};
  int32_t                    ret = 0;

  (void)memset(val, 0x0, sizeof(lsm6dsv16x_pin_int_route_t));

  ret = lsm6dsv16x_read_reg(ctx, LSM6DSV16X_INT1_CTRL, (uint8_t *)&int1_ctrl, 1);
  ret += lsm6dsv16x_read_reg(ctx, LSM6DSV16X_MD1_CFG, (uint8_t *)&md1_cfg, 1);
  if (ret != 0)
  {
    return ret;
  }

  val->drdy_xl   = int1_ctrl.int1_drdy_xl;
  val->drdy_g    = int1_ctrl.int1_drdy_g;
  val->fifo_th   = int1_ctrl.int1_fifo_th;
  val->fifo_ovr  = int1_ctrl.int1_fifo_ovr;
  val->fifo_full = int1_ctrl.int1_fifo_full;
  val->cnt_bdr   = int1_ctrl.int1_cnt_bdr;

  val->shub         = md1_cfg.int1_shub;
  val->emb_func     = md1_cfg.int1_emb_func;
  val->sixd         = md1_cfg.int1_6d;
  val->single_tap   = md1_cfg.int1_single_tap;
  val->double_tap   = md1_cfg.int1_double_tap;
  val->wakeup       = md1_cfg.int1_wu;
  val->freefall     = md1_cfg.int1_ff;
  val->sleep_change = md1_cfg.int1_sleep_change;

  return ret;
}


int32_t lsm6dsv16x_pin_int2_route_set(const stmdev_ctx_t *ctx,
                                      lsm6dsv16x_pin_int_route_t *val)
{
  lsm6dsv16x_int2_ctrl_t          int2_ctrl = {0};
  lsm6dsv16x_ctrl4_t              ctrl4 = {0};
  lsm6dsv16x_ctrl7_t              ctrl7 = {0};
  lsm6dsv16x_md2_cfg_t            md2_cfg = {0};
  int32_t                    ret = 0;

  ret = lsm6dsv16x_read_reg(ctx, LSM6DSV16X_INT2_CTRL, (uint8_t *)&int2_ctrl, 1);
  if (ret != 0)
  {
    return ret;
  }

  int2_ctrl.int2_drdy_xl          = val->drdy_xl;
  int2_ctrl.int2_drdy_g           = val->drdy_g;
  int2_ctrl.int2_fifo_th          = val->fifo_th;
  int2_ctrl.int2_fifo_ovr         = val->fifo_ovr;
  int2_ctrl.int2_fifo_full        = val->fifo_full;
  int2_ctrl.int2_cnt_bdr          = val->cnt_bdr;
  int2_ctrl.int2_drdy_g_eis       = val->drdy_g_eis;
  int2_ctrl.int2_emb_func_endop   = val->emb_func_endop;

  ret = lsm6dsv16x_write_reg(ctx, LSM6DSV16X_INT2_CTRL, (uint8_t *)&int2_ctrl, 1);

  ret += lsm6dsv16x_read_reg(ctx, LSM6DSV16X_CTRL4, (uint8_t *)&ctrl4, 1);
  if (ret != 0)
  {
    return ret;
  }
  ctrl4.int2_drdy_temp         = val->drdy_temp;
  ret += lsm6dsv16x_write_reg(ctx, LSM6DSV16X_CTRL4, (uint8_t *)&ctrl4, 1);
  if (ret != 0)
  {
    return ret;
  }

  ret = lsm6dsv16x_read_reg(ctx, LSM6DSV16X_CTRL7, (uint8_t *)&ctrl7, 1);
  if (ret != 0)
  {
    return ret;
  }
  ctrl7.int2_drdy_ah_qvar         = val->drdy_ah_qvar;
  ret += lsm6dsv16x_write_reg(ctx, LSM6DSV16X_CTRL7, (uint8_t *)&ctrl7, 1);
  if (ret != 0)
  {
    return ret;
  }

  ret = lsm6dsv16x_read_reg(ctx, LSM6DSV16X_MD2_CFG, (uint8_t *)&md2_cfg, 1);
  if (ret != 0)
  {
    return ret;
  }

  md2_cfg.int2_timestamp       = val->timestamp;
  md2_cfg.int2_emb_func        = val->emb_func;
  md2_cfg.int2_6d              = val->sixd;
  md2_cfg.int2_single_tap      = val->single_tap;
  md2_cfg.int2_double_tap      = val->double_tap;
  md2_cfg.int2_wu              = val->wakeup;
  md2_cfg.int2_ff              = val->freefall;
  md2_cfg.int2_sleep_change    = val->sleep_change;

  ret = lsm6dsv16x_write_reg(ctx, LSM6DSV16X_MD2_CFG, (uint8_t *)&md2_cfg, 1);

  return ret;
}


int32_t lsm6dsv16x_pin_int2_route_get(const stmdev_ctx_t *ctx,
                                      lsm6dsv16x_pin_int_route_t *val)
{
  lsm6dsv16x_int2_ctrl_t          int2_ctrl = {0};
  lsm6dsv16x_ctrl4_t              ctrl4 = {0};
  lsm6dsv16x_ctrl7_t              ctrl7 = {0};
  lsm6dsv16x_md2_cfg_t            md2_cfg = {0};
  int32_t                    ret = 0;

  (void)memset(val, 0x0, sizeof(lsm6dsv16x_pin_int_route_t));

  ret = lsm6dsv16x_read_reg(ctx, LSM6DSV16X_INT2_CTRL, (uint8_t *)&int2_ctrl, 1);
  if (ret != 0)
  {
    return ret;
  }

  val->drdy_xl        = int2_ctrl.int2_drdy_xl;
  val->drdy_g         = int2_ctrl.int2_drdy_g;
  val->fifo_th        = int2_ctrl.int2_fifo_th;
  val->fifo_ovr       = int2_ctrl.int2_fifo_ovr;
  val->fifo_full      = int2_ctrl.int2_fifo_full;
  val->cnt_bdr        = int2_ctrl.int2_cnt_bdr;
  val->drdy_g_eis     = int2_ctrl.int2_drdy_g_eis;
  val->emb_func_endop = int2_ctrl.int2_emb_func_endop;

  ret = lsm6dsv16x_read_reg(ctx, LSM6DSV16X_CTRL4, (uint8_t *)&ctrl4, 1);
  if (ret != 0)
  {
    return ret;
  }

  val->drdy_temp      = ctrl4.int2_drdy_temp;

  ret = lsm6dsv16x_read_reg(ctx, LSM6DSV16X_CTRL7, (uint8_t *)&ctrl7, 1);
  if (ret != 0)
  {
    return ret;
  }

  val->drdy_ah_qvar = ctrl7.int2_drdy_ah_qvar;

  ret = lsm6dsv16x_read_reg(ctx, LSM6DSV16X_MD2_CFG, (uint8_t *)&md2_cfg, 1);
  if (ret != 0)
  {
    return ret;
  }

  val->timestamp      = md2_cfg.int2_timestamp;
  val->emb_func       = md2_cfg.int2_emb_func;
  val->sixd           = md2_cfg.int2_6d;
  val->single_tap     = md2_cfg.int2_single_tap;
  val->double_tap     = md2_cfg.int2_double_tap;
  val->wakeup         = md2_cfg.int2_wu;
  val->freefall       = md2_cfg.int2_ff;
  val->sleep_change   = md2_cfg.int2_sleep_change;

  return ret;
}


int32_t lsm6dsv16x_emb_pin_int1_route_set(const stmdev_ctx_t *ctx,
                                          const lsm6dsv16x_emb_pin_int_route_t *val)
{
  lsm6dsv16x_emb_func_int1_t emb_func_int1 = {0};
  lsm6dsv16x_md1_cfg_t md1_cfg = {0};
  int32_t ret = 0;

  ret = lsm6dsv16x_mem_bank_set(ctx, LSM6DSV16X_EMBED_FUNC_MEM_BANK);
  if (ret != 0)
  {
    return ret;
  }

  ret = lsm6dsv16x_read_reg(ctx, LSM6DSV16X_EMB_FUNC_INT1, (uint8_t *)&emb_func_int1, 1);

  if (ret == 0)
  {
    emb_func_int1.int1_tilt = val->tilt;
    emb_func_int1.int1_sig_mot = val->sig_mot;
    emb_func_int1.int1_step_detector = val->step_det;
    emb_func_int1.int1_fsm_lc = val->fsm_lc;

    ret = lsm6dsv16x_write_reg(ctx, LSM6DSV16X_EMB_FUNC_INT1, (uint8_t *)&emb_func_int1, 1);
  }
  ret += lsm6dsv16x_mem_bank_set(ctx, LSM6DSV16X_MAIN_MEM_BANK);

  ret += lsm6dsv16x_read_reg(ctx, LSM6DSV16X_MD1_CFG, (uint8_t *)&md1_cfg, 1);
  if (ret == 0)
  {
    md1_cfg.int1_emb_func = 1;
    ret = lsm6dsv16x_write_reg(ctx, LSM6DSV16X_MD1_CFG, (uint8_t *)&md1_cfg, 1);
  }

  return ret;
}


int32_t lsm6dsv16x_emb_pin_int1_route_get(const stmdev_ctx_t *ctx,
                                          lsm6dsv16x_emb_pin_int_route_t *val)
{
  lsm6dsv16x_emb_func_int1_t emb_func_int1 = {0};
  int32_t ret = 0;

  ret = lsm6dsv16x_mem_bank_set(ctx, LSM6DSV16X_EMBED_FUNC_MEM_BANK);
  if (ret != 0)
  {
    return ret;
  }

  ret = lsm6dsv16x_read_reg(ctx, LSM6DSV16X_EMB_FUNC_INT1, (uint8_t *)&emb_func_int1, 1);

  if (ret == 0)
  {
    val->tilt = emb_func_int1.int1_tilt;
    val->sig_mot = emb_func_int1.int1_sig_mot;
    val->step_det = emb_func_int1.int1_step_detector;
    val->fsm_lc = emb_func_int1.int1_fsm_lc;
  }
  ret = lsm6dsv16x_mem_bank_set(ctx, LSM6DSV16X_MAIN_MEM_BANK);

  return ret;
}


int32_t lsm6dsv16x_emb_pin_int2_route_set(const stmdev_ctx_t *ctx,
                                          const lsm6dsv16x_emb_pin_int_route_t *val)
{
  lsm6dsv16x_emb_func_int2_t emb_func_int2 = {0};
  lsm6dsv16x_md2_cfg_t md2_cfg = {0};
  int32_t ret = 0;

  ret = lsm6dsv16x_mem_bank_set(ctx, LSM6DSV16X_EMBED_FUNC_MEM_BANK);
  if (ret != 0)
  {
    return ret;
  }

  ret = lsm6dsv16x_read_reg(ctx, LSM6DSV16X_EMB_FUNC_INT2, (uint8_t *)&emb_func_int2, 1);

  if (ret == 0)
  {
    emb_func_int2.int2_tilt = val->tilt;
    emb_func_int2.int2_sig_mot = val->sig_mot;
    emb_func_int2.int2_step_detector = val->step_det;
    emb_func_int2.int2_fsm_lc = val->fsm_lc;

    ret = lsm6dsv16x_write_reg(ctx, LSM6DSV16X_EMB_FUNC_INT2, (uint8_t *)&emb_func_int2, 1);
  }
  ret += lsm6dsv16x_mem_bank_set(ctx, LSM6DSV16X_MAIN_MEM_BANK);

  ret += lsm6dsv16x_read_reg(ctx, LSM6DSV16X_MD2_CFG, (uint8_t *)&md2_cfg, 1);
  if (ret == 0)
  {
    md2_cfg.int2_emb_func = 1;
    ret = lsm6dsv16x_write_reg(ctx, LSM6DSV16X_MD2_CFG, (uint8_t *)&md2_cfg, 1);
  }

  return ret;
}


int32_t lsm6dsv16x_emb_pin_int2_route_get(const stmdev_ctx_t *ctx,
                                          lsm6dsv16x_emb_pin_int_route_t *val)
{
  lsm6dsv16x_emb_func_int2_t emb_func_int2 = {0};
  int32_t ret = 0;

  ret = lsm6dsv16x_mem_bank_set(ctx, LSM6DSV16X_EMBED_FUNC_MEM_BANK);
  if (ret != 0)
  {
    return ret;
  }

  ret = lsm6dsv16x_read_reg(ctx, LSM6DSV16X_EMB_FUNC_INT2, (uint8_t *)&emb_func_int2, 1);

  if (ret == 0)
  {
    val->tilt = emb_func_int2.int2_tilt;
    val->sig_mot = emb_func_int2.int2_sig_mot;
    val->step_det = emb_func_int2.int2_step_detector;
    val->fsm_lc = emb_func_int2.int2_fsm_lc;
  }
  ret = lsm6dsv16x_mem_bank_set(ctx, LSM6DSV16X_MAIN_MEM_BANK);

  return ret;
}


int32_t lsm6dsv16x_embedded_int_cfg_set(const stmdev_ctx_t *ctx,
                                        lsm6dsv16x_embedded_int_config_t val)
{
  lsm6dsv16x_page_rw_t page_rw = {0};
  int32_t ret = 0;

  ret = lsm6dsv16x_mem_bank_set(ctx, LSM6DSV16X_EMBED_FUNC_MEM_BANK);
  if (ret != 0)
  {
    return ret;
  }

  ret = lsm6dsv16x_read_reg(ctx, LSM6DSV16X_PAGE_RW, (uint8_t *)&page_rw, 1);

  if (ret == 0)
  {
    switch (val)
    {
      case 0x00:
        page_rw.emb_func_lir = 0;
        break;

      case 0x01:
      default:
        page_rw.emb_func_lir = 1;
        break;
    }

    ret += lsm6dsv16x_write_reg(ctx, LSM6DSV16X_PAGE_RW, (uint8_t *)&page_rw, 1);
  }

  ret += lsm6dsv16x_mem_bank_set(ctx, LSM6DSV16X_MAIN_MEM_BANK);

  return ret;
}


int32_t lsm6dsv16x_embedded_int_cfg_get(const stmdev_ctx_t *ctx,
                                        lsm6dsv16x_embedded_int_config_t *val)
{
  lsm6dsv16x_page_rw_t page_rw = {0};
  int32_t ret = 0;

  ret = lsm6dsv16x_mem_bank_set(ctx, LSM6DSV16X_EMBED_FUNC_MEM_BANK);
  if (ret != 0)
  {
    return ret;
  }

  ret = lsm6dsv16x_read_reg(ctx, LSM6DSV16X_PAGE_RW, (uint8_t *)&page_rw, 1);

  if (ret == 0)
  {
    if (page_rw.emb_func_lir == 0U)
    {
      *val = LSM6DSV16X_INT_LATCH_DISABLE;
    }
    else
    {
      *val = LSM6DSV16X_INT_LATCH_ENABLE;
    }
  }

  ret += lsm6dsv16x_mem_bank_set(ctx, LSM6DSV16X_MAIN_MEM_BANK);

  return ret;
}


int32_t lsm6dsv16x_embedded_status_get(const stmdev_ctx_t *ctx,
                                       lsm6dsv16x_embedded_status_t *val)
{
  lsm6dsv16x_emb_func_status_mainpage_t emb_func_status = {0};
  lsm6dsv16x_emb_func_src_t emb_func_src = {0};
  int32_t ret = 0;

  ret = lsm6dsv16x_read_reg(ctx, LSM6DSV16X_EMB_FUNC_STATUS_MAINPAGE, (uint8_t *)&emb_func_status, 1);
  if (ret != 0)
  {
    return ret;
  }

  val->step_detector = emb_func_status.is_step_det;
  val->tilt = emb_func_status.is_tilt;
  val->sig_mot = emb_func_status.is_sigmot;
  val->fsm_lc = emb_func_status.is_fsm_lc;

  /* embedded func */
  ret = lsm6dsv16x_mem_bank_set(ctx, LSM6DSV16X_EMBED_FUNC_MEM_BANK);
  if (ret != 0)
  {
    return ret;
  }
  ret += lsm6dsv16x_read_reg(ctx, LSM6DSV16X_EMB_FUNC_SRC, (uint8_t *)&emb_func_src, 1);
  ret += lsm6dsv16x_mem_bank_set(ctx, LSM6DSV16X_MAIN_MEM_BANK);
  if (ret != 0)
  {
    return ret;
  }

  val->step_count_inc = emb_func_src.stepcounter_bit_set;
  val->step_count_overflow = emb_func_src.step_overflow;
  val->step_on_delta_time = emb_func_src.step_count_delta_ia;
  val->step_detector = emb_func_src.step_detected;

  return ret;
}

int32_t lsm6dsv16x_all_sources_get(const stmdev_ctx_t *ctx,
                                   lsm6dsv16x_all_sources_t *val)
{
  lsm6dsv16x_emb_func_status_mainpage_t emb_func_status_mainpage = {0};
  lsm6dsv16x_emb_func_exec_status_t emb_func_exec_status = {0};
  lsm6dsv16x_fsm_status_mainpage_t fsm_status_mainpage = {0};
  lsm6dsv16x_mlc_status_mainpage_t mlc_status_mainpage = {0};
  lsm6dsv16x_functions_enable_t functions_enable = {0};
  lsm6dsv16x_emb_func_src_t emb_func_src = {0};
  lsm6dsv16x_fifo_status2_t fifo_status2 = {0};
  lsm6dsv16x_all_int_src_t all_int_src = {0};
  lsm6dsv16x_wake_up_src_t wake_up_src = {0};
  lsm6dsv16x_status_reg_t status_reg = {0};
  lsm6dsv16x_d6d_src_t d6d_src = {0};
  lsm6dsv16x_tap_src_t tap_src = {0};
  lsm6dsv16x_ui_status_reg_ois_t status_reg_ois = {0};
  lsm6dsv16x_status_master_t status_shub = {0};
  uint8_t buff[8] = {0};
  int32_t ret = {0};

  ret = lsm6dsv16x_read_reg(ctx, LSM6DSV16X_FUNCTIONS_ENABLE, (uint8_t *)&functions_enable, 1);
  if (ret != 0)
  {
    return ret;
  }
  functions_enable.dis_rst_lir_all_int = PROPERTY_ENABLE;
  ret = lsm6dsv16x_write_reg(ctx, LSM6DSV16X_FUNCTIONS_ENABLE, (uint8_t *)&functions_enable, 1);

  ret += lsm6dsv16x_read_reg(ctx, LSM6DSV16X_FIFO_STATUS1, (uint8_t *)&buff, 4);

  bytecpy((uint8_t *)&fifo_status2, &buff[1]);
  bytecpy((uint8_t *)&all_int_src, &buff[2]);
  bytecpy((uint8_t *)&status_reg, &buff[3]);

  val->fifo_ovr = fifo_status2.fifo_ovr_ia;
  val->fifo_bdr = fifo_status2.counter_bdr_ia;
  val->fifo_full = fifo_status2.fifo_full_ia;
  val->fifo_th = fifo_status2.fifo_wtm_ia;

  val->free_fall = all_int_src.ff_ia;
  val->wake_up = all_int_src.wu_ia;
  val->six_d = all_int_src.d6d_ia;

  val->drdy_xl = status_reg.xlda;
  val->drdy_gy = status_reg.gda;
  val->drdy_temp = status_reg.tda;
  val->drdy_ah_qvar = status_reg.ah_qvarda;
  val->drdy_eis = status_reg.gda_eis;
  val->drdy_ois = status_reg.ois_drdy;
  val->timestamp = status_reg.timestamp_endcount;

  ret = lsm6dsv16x_read_reg(ctx, LSM6DSV16X_FUNCTIONS_ENABLE, (uint8_t *)&functions_enable, 1);
  functions_enable.dis_rst_lir_all_int = PROPERTY_DISABLE;
  ret += lsm6dsv16x_write_reg(ctx, LSM6DSV16X_FUNCTIONS_ENABLE, (uint8_t *)&functions_enable, 1);
  if (ret != 0)
  {
    return ret;
  }

  ret = lsm6dsv16x_read_reg(ctx, LSM6DSV16X_UI_STATUS_REG_OIS, (uint8_t *)&buff, 8);
  if (ret != 0)
  {
    return ret;
  }

  bytecpy((uint8_t *)&status_reg_ois, &buff[0]);
  bytecpy((uint8_t *)&wake_up_src, &buff[1]);
  bytecpy((uint8_t *)&tap_src, &buff[2]);
  bytecpy((uint8_t *)&d6d_src, &buff[3]);
  bytecpy((uint8_t *)&emb_func_status_mainpage, &buff[5]);
  bytecpy((uint8_t *)&fsm_status_mainpage, &buff[6]);
  bytecpy((uint8_t *)&mlc_status_mainpage, &buff[7]);

  val->gy_settling = status_reg_ois.gyro_settling;
  val->sleep_change = wake_up_src.sleep_change_ia;
  val->wake_up_x = wake_up_src.x_wu;
  val->wake_up_y = wake_up_src.y_wu;
  val->wake_up_z = wake_up_src.z_wu;
  val->sleep_state = wake_up_src.sleep_state;

  val->tap_x = tap_src.x_tap;
  val->tap_y = tap_src.y_tap;
  val->tap_z = tap_src.z_tap;
  val->tap_sign = tap_src.tap_sign;
  val->double_tap = tap_src.double_tap;
  val->single_tap = tap_src.single_tap;

  val->six_d_zl = d6d_src.zl;
  val->six_d_zh = d6d_src.zh;
  val->six_d_yl = d6d_src.yl;
  val->six_d_yh = d6d_src.yh;
  val->six_d_xl = d6d_src.xl;
  val->six_d_xh = d6d_src.xh;

  val->step_detector = emb_func_status_mainpage.is_step_det;
  val->tilt = emb_func_status_mainpage.is_tilt;
  val->sig_mot = emb_func_status_mainpage.is_sigmot;
  val->fsm_lc = emb_func_status_mainpage.is_fsm_lc;

  val->fsm1 = fsm_status_mainpage.is_fsm1;
  val->fsm2 = fsm_status_mainpage.is_fsm2;
  val->fsm3 = fsm_status_mainpage.is_fsm3;
  val->fsm4 = fsm_status_mainpage.is_fsm4;
  val->fsm5 = fsm_status_mainpage.is_fsm5;
  val->fsm6 = fsm_status_mainpage.is_fsm6;
  val->fsm7 = fsm_status_mainpage.is_fsm7;
  val->fsm8 = fsm_status_mainpage.is_fsm8;

  val->mlc1 = mlc_status_mainpage.is_mlc1;
  val->mlc2 = mlc_status_mainpage.is_mlc2;
  val->mlc3 = mlc_status_mainpage.is_mlc3;
  val->mlc4 = mlc_status_mainpage.is_mlc4;

  /* embedded func */
  ret = lsm6dsv16x_mem_bank_set(ctx, LSM6DSV16X_EMBED_FUNC_MEM_BANK);
  if (ret == 0)
  {
    ret = lsm6dsv16x_read_reg(ctx, LSM6DSV16X_EMB_FUNC_EXEC_STATUS, (uint8_t *)&emb_func_exec_status,
                              1);
    ret += lsm6dsv16x_read_reg(ctx, LSM6DSV16X_EMB_FUNC_SRC, (uint8_t *)&emb_func_src, 1);
  }
  ret += lsm6dsv16x_mem_bank_set(ctx, LSM6DSV16X_MAIN_MEM_BANK);
  if (ret != 0)
  {
    return ret;
  }

  val->emb_func_stand_by = emb_func_exec_status.emb_func_endop;
  val->emb_func_time_exceed = emb_func_exec_status.emb_func_exec_ovr;
  val->step_count_inc = emb_func_src.stepcounter_bit_set;
  val->step_count_overflow = emb_func_src.step_overflow;
  val->step_on_delta_time = emb_func_src.step_count_delta_ia;

  val->step_detector = emb_func_src.step_detected;

  /* sensor hub */
  ret = lsm6dsv16x_read_reg(ctx, LSM6DSV16X_STATUS_MASTER_MAINPAGE, (uint8_t *)&status_shub, 1);
  if (ret != 0)
  {
    return ret;
  }

  val->sh_endop = status_shub.sens_hub_endop;
  val->sh_wr_once = status_shub.wr_once_done;
  val->sh_slave3_nack = status_shub.slave3_nack;
  val->sh_slave2_nack = status_shub.slave2_nack;
  val->sh_slave1_nack = status_shub.slave1_nack;
  val->sh_slave0_nack = status_shub.slave0_nack;

  return ret;
}

int32_t lsm6dsv16x_flag_data_ready_get(const stmdev_ctx_t *ctx,
                                       lsm6dsv16x_data_ready_t *val)
{
  lsm6dsv16x_status_reg_t status = {0};
  int32_t ret = 0;

  ret = lsm6dsv16x_read_reg(ctx, LSM6DSV16X_STATUS_REG, (uint8_t *)&status, 1);
  if (ret != 0)
  {
    return ret;
  }

  val->drdy_xl = status.xlda;
  val->drdy_gy = status.gda;
  val->drdy_temp = status.tda;

  return ret;
}


int32_t lsm6dsv16x_int_ack_mask_set(const stmdev_ctx_t *ctx, uint8_t val)
{
  int32_t ret = 0;

  ret = lsm6dsv16x_write_reg(ctx, LSM6DSV16X_INT_ACK_MASK, &val, 1);

  return ret;
}

int32_t lsm6dsv16x_int_ack_mask_get(const stmdev_ctx_t *ctx, uint8_t *val)
{
  int32_t ret = 0;

  ret = lsm6dsv16x_read_reg(ctx, LSM6DSV16X_INT_ACK_MASK, val, 1);

  return ret;
}


int32_t lsm6dsv16x_temperature_raw_get(const stmdev_ctx_t *ctx, int16_t *val)
{
  uint8_t buff[2] = {0};
  int32_t ret = 0;

  ret = lsm6dsv16x_read_reg(ctx, LSM6DSV16X_OUT_TEMP_L, &buff[0], 2);
  if (ret != 0)
  {
    return ret;
  }

  *val = (int16_t)buff[1];
  *val = (*val * 256) + (int16_t)buff[0];

  return ret;
}


int32_t lsm6dsv16x_angular_rate_raw_get(const stmdev_ctx_t *ctx, int16_t *val)
{
  uint8_t buff[6] = {0};
  int32_t ret = 0;

  ret = lsm6dsv16x_read_reg(ctx, LSM6DSV16X_OUTX_L_G, &buff[0], 6);
  if (ret != 0)
  {
    return ret;
  }

  val[0] = (int16_t)(((uint16_t)buff[1] << 8) | (uint16_t)buff[0]);
  val[1] = (int16_t)(((uint16_t)buff[3] << 8) | (uint16_t)buff[2]);
  val[2] = (int16_t)(((uint16_t)buff[5] << 8) | (uint16_t)buff[4]);

  return ret;
}


int32_t lsm6dsv16x_ois_angular_rate_raw_get(const stmdev_ctx_t *ctx, int16_t *val)
{
  uint8_t buff[6] = {0};
  int32_t ret = 0;

  ret = lsm6dsv16x_read_reg(ctx, LSM6DSV16X_SPI2_OUTX_L_G_OIS, &buff[0], 6);
  if (ret != 0)
  {
    return ret;
  }

  val[0] = (int16_t)(((uint16_t)buff[1] << 8) | (uint16_t)buff[0]);
  val[1] = (int16_t)(((uint16_t)buff[3] << 8) | (uint16_t)buff[2]);
  val[2] = (int16_t)(((uint16_t)buff[5] << 8) | (uint16_t)buff[4]);

  return ret;
}


int32_t lsm6dsv16x_ois_eis_angular_rate_raw_get(const stmdev_ctx_t *ctx, int16_t *val)
{
  uint8_t buff[6] = {0};
  int32_t ret = 0;

  ret = lsm6dsv16x_read_reg(ctx, LSM6DSV16X_UI_OUTX_L_G_OIS_EIS, &buff[0], 6);
  if (ret != 0)
  {
    return ret;
  }

  val[0] = (int16_t)((int16_t)buff[1] * 256) + (int16_t)buff[0];
  val[1] = (int16_t)((int16_t)buff[3] * 256) + (int16_t)buff[2];
  val[2] = (int16_t)((int16_t)buff[5] * 256) + (int16_t)buff[4];

  return ret;
}


int32_t lsm6dsv16x_acceleration_raw_get(const stmdev_ctx_t *ctx, int16_t *val)
{
  uint8_t buff[6] = {0};
  int32_t ret = 0;

  ret = lsm6dsv16x_read_reg(ctx, LSM6DSV16X_OUTX_L_A, &buff[0], 6);
  if (ret != 0)
  {
    return ret;
  }

  val[0] = (int16_t)buff[1];
  val[0] = (val[0] * 256) + (int16_t)buff[0];
  val[1] = (int16_t)buff[3];
  val[1] = (val[1] * 256) + (int16_t)buff[2];
  val[2] = (int16_t)buff[5];
  val[2] = (val[2] * 256) + (int16_t)buff[4];

  return ret;
}


int32_t lsm6dsv16x_dual_acceleration_raw_get(const stmdev_ctx_t *ctx, int16_t *val)
{
  uint8_t buff[6] = {0};
  int32_t ret = 0;

  ret = lsm6dsv16x_read_reg(ctx, LSM6DSV16X_UI_OUTX_L_A_OIS_DUALC, &buff[0], 6);
  if (ret != 0)
  {
    return ret;
  }

  val[0] = (int16_t)buff[1];
  val[0] = (val[0] * 256) + (int16_t)buff[0];
  val[1] = (int16_t)buff[3];
  val[1] = (val[1] * 256) + (int16_t)buff[2];
  val[2] = (int16_t)buff[5];
  val[2] = (val[2] * 256) + (int16_t)buff[4];

  return ret;
}

int32_t lsm6dsv16x_ah_qvar_raw_get(const stmdev_ctx_t *ctx, int16_t *val)
{
  uint8_t buff[2] = {0};
  int32_t ret = 0;

  ret = lsm6dsv16x_read_reg(ctx, LSM6DSV16X_AH_QVAR_OUT_L, &buff[0], 2);
  if (ret != 0)
  {
    return ret;
  }

  *val = (int16_t)buff[1];
  *val = (*val * 256) + (int16_t)buff[0];

  return ret;
}


int32_t lsm6dsv16x_odr_cal_reg_get(const stmdev_ctx_t *ctx, int8_t *val)
{
  lsm6dsv16x_internal_freq_t internal_freq = {0};
  int32_t ret = 0;

  ret = lsm6dsv16x_read_reg(ctx, LSM6DSV16X_INTERNAL_FREQ, (uint8_t *)&internal_freq, 1);
  if (ret != 0)
  {
    return ret;
  }

  *val = (int8_t)internal_freq.freq_fine;

  return ret;
}

int32_t lsm6dsv16x_ln_pg_write(const stmdev_ctx_t *ctx, uint16_t address,
                               uint8_t *buf, uint8_t len)
{
  lsm6dsv16x_page_address_t  page_address = {0};
  lsm6dsv16x_page_sel_t page_sel = {0};
  lsm6dsv16x_page_rw_t page_rw = {0};
  uint8_t msb = 0;
  uint8_t lsb = 0;
  int32_t ret = 0;
  uint8_t i = 0;

  msb = ((uint8_t)(address >> 8) & 0x0FU);
  lsb = (uint8_t)address & 0xFFU;

  ret = lsm6dsv16x_mem_bank_set(ctx, LSM6DSV16X_EMBED_FUNC_MEM_BANK);
  if (ret != 0)
  {
    return ret;
  }

  /* set page write */
  ret += lsm6dsv16x_read_reg(ctx, LSM6DSV16X_PAGE_RW, (uint8_t *)&page_rw, 1);
  if (ret != 0)
  {
    goto exit;
  }
  page_rw.page_read = PROPERTY_DISABLE;
  page_rw.page_write = PROPERTY_ENABLE;
  ret += lsm6dsv16x_write_reg(ctx, LSM6DSV16X_PAGE_RW, (uint8_t *)&page_rw, 1);
  if (ret != 0)
  {
    goto exit;
  }

  /* select page */
  ret += lsm6dsv16x_read_reg(ctx, LSM6DSV16X_PAGE_SEL, (uint8_t *)&page_sel, 1);
  if (ret != 0)
  {
    goto exit;
  }
  page_sel.page_sel = msb;
  page_sel.not_used0 = 1; // Default value
  ret += lsm6dsv16x_write_reg(ctx, LSM6DSV16X_PAGE_SEL, (uint8_t *)&page_sel, 1);
  if (ret != 0)
  {
    goto exit;
  }

  /* set page addr */
  page_address.page_addr = lsb;
  ret += lsm6dsv16x_write_reg(ctx, LSM6DSV16X_PAGE_ADDRESS,
                              (uint8_t *)&page_address, 1);
  if (ret != 0)
  {
    goto exit;
  }

  for (i = 0; i < len; i++)
  {
    ret += lsm6dsv16x_write_reg(ctx, LSM6DSV16X_PAGE_VALUE, &buf[i], 1);
    if (ret != 0)
    {
      goto exit;
    }

    lsb++;

    /* Check if page wrap */
    if ((lsb & 0xFFU) == 0x00U)
    {
      msb++;
      ret += lsm6dsv16x_read_reg(ctx, LSM6DSV16X_PAGE_SEL, (uint8_t *)&page_sel, 1);
      if (ret != 0)
      {
        goto exit;
      }

      page_sel.page_sel = msb;
      page_sel.not_used0 = 1; // Default value
      ret += lsm6dsv16x_write_reg(ctx, LSM6DSV16X_PAGE_SEL, (uint8_t *)&page_sel, 1);
      if (ret != 0)
      {
        goto exit;
      }
    }
  }

  page_sel.page_sel = 0;
  page_sel.not_used0 = 1;// Default value
  ret += lsm6dsv16x_write_reg(ctx, LSM6DSV16X_PAGE_SEL, (uint8_t *)&page_sel, 1);
  if (ret != 0)
  {
    goto exit;
  }

  /* unset page write */
  ret += lsm6dsv16x_read_reg(ctx, LSM6DSV16X_PAGE_RW, (uint8_t *)&page_rw, 1);
  if (ret != 0)
  {
    goto exit;
  }
  page_rw.page_read = PROPERTY_DISABLE;
  page_rw.page_write = PROPERTY_DISABLE;
  ret += lsm6dsv16x_write_reg(ctx, LSM6DSV16X_PAGE_RW, (uint8_t *)&page_rw, 1);

exit:
  ret += lsm6dsv16x_mem_bank_set(ctx, LSM6DSV16X_MAIN_MEM_BANK);

  return ret;
}


int32_t lsm6dsv16x_ln_pg_read(const stmdev_ctx_t *ctx, uint16_t address, uint8_t *buf,
                              uint8_t len)
{
  lsm6dsv16x_page_address_t page_address = {0};
  lsm6dsv16x_page_sel_t page_sel = {0};
  lsm6dsv16x_page_rw_t page_rw = {0};
  uint8_t msb = 0;
  uint8_t lsb = 0;
  int32_t ret = 0;
  uint8_t i = 0;

  msb = ((uint8_t)(address >> 8) & 0x0FU);
  lsb = (uint8_t)address & 0xFFU;

  ret = lsm6dsv16x_mem_bank_set(ctx, LSM6DSV16X_EMBED_FUNC_MEM_BANK);
  if (ret != 0)
  {
    return ret;
  }

  /* set page write */
  ret += lsm6dsv16x_read_reg(ctx, LSM6DSV16X_PAGE_RW, (uint8_t *)&page_rw, 1);
  if (ret != 0)
  {
    goto exit;
  }
  page_rw.page_read = PROPERTY_ENABLE;
  page_rw.page_write = PROPERTY_DISABLE;
  ret += lsm6dsv16x_write_reg(ctx, LSM6DSV16X_PAGE_RW, (uint8_t *)&page_rw, 1);
  if (ret != 0)
  {
    goto exit;
  }

  /* select page */
  ret += lsm6dsv16x_read_reg(ctx, LSM6DSV16X_PAGE_SEL, (uint8_t *)&page_sel, 1);
  if (ret != 0)
  {
    goto exit;
  }
  page_sel.page_sel = msb;
  page_sel.not_used0 = 1; // Default value
  ret += lsm6dsv16x_write_reg(ctx, LSM6DSV16X_PAGE_SEL, (uint8_t *)&page_sel, 1);
  if (ret != 0)
  {
    goto exit;
  }

  /* set page addr */
  page_address.page_addr = lsb;
  ret += lsm6dsv16x_write_reg(ctx, LSM6DSV16X_PAGE_ADDRESS,
                              (uint8_t *)&page_address, 1);
  if (ret != 0)
  {
    goto exit;
  }

  for (i = 0; i < len; i++)
  {
    ret += lsm6dsv16x_read_reg(ctx, LSM6DSV16X_PAGE_VALUE, &buf[i], 1);
    if (ret != 0)
    {
      goto exit;
    }

    lsb++;

    /* Check if page wrap */
    if ((lsb & 0xFFU) == 0x00U)
    {
      msb++;
      ret += lsm6dsv16x_read_reg(ctx, LSM6DSV16X_PAGE_SEL, (uint8_t *)&page_sel, 1);
      if (ret != 0)
      {
        goto exit;
      }

      page_sel.page_sel = msb;
      page_sel.not_used0 = 1; // Default value
      ret += lsm6dsv16x_write_reg(ctx, LSM6DSV16X_PAGE_SEL, (uint8_t *)&page_sel, 1);
      if (ret != 0)
      {
        goto exit;
      }
    }
  }

  page_sel.page_sel = 0;
  page_sel.not_used0 = 1;// Default value
  ret += lsm6dsv16x_write_reg(ctx, LSM6DSV16X_PAGE_SEL, (uint8_t *)&page_sel, 1);
  if (ret != 0)
  {
    goto exit;
  }

  /* unset page write */
  ret += lsm6dsv16x_read_reg(ctx, LSM6DSV16X_PAGE_RW, (uint8_t *)&page_rw, 1);
  if (ret != 0)
  {
    goto exit;
  }
  page_rw.page_read = PROPERTY_DISABLE;
  page_rw.page_write = PROPERTY_DISABLE;
  ret += lsm6dsv16x_write_reg(ctx, LSM6DSV16X_PAGE_RW, (uint8_t *)&page_rw, 1);

exit:
  ret += lsm6dsv16x_mem_bank_set(ctx, LSM6DSV16X_MAIN_MEM_BANK);

  return ret;
}


int32_t lsm6dsv16x_emb_function_dbg_set(const stmdev_ctx_t *ctx, uint8_t val)
{
  lsm6dsv16x_ctrl10_t ctrl10 = {0};
  int32_t ret = 0;

  ret = lsm6dsv16x_read_reg(ctx, LSM6DSV16X_CTRL10, (uint8_t *)&ctrl10, 1);

  if (ret == 0)
  {
    ctrl10.emb_func_debug = val;
    ret = lsm6dsv16x_write_reg(ctx, LSM6DSV16X_CTRL10, (uint8_t *)&ctrl10, 1);
  }

  return ret;
}


int32_t lsm6dsv16x_emb_function_dbg_get(const stmdev_ctx_t *ctx, uint8_t *val)
{
  lsm6dsv16x_ctrl10_t ctrl10 = {0};
  int32_t ret = 0;

  ret = lsm6dsv16x_read_reg(ctx, LSM6DSV16X_CTRL10, (uint8_t *)&ctrl10, 1);
  if (ret != 0)
  {
    return ret;
  }

  *val = ctrl10.emb_func_debug;

  return ret;
}


int32_t lsm6dsv16x_den_polarity_set(const stmdev_ctx_t *ctx,
                                    lsm6dsv16x_den_polarity_t val)
{
  lsm6dsv16x_ctrl4_t ctrl4 = {0};
  int32_t ret = 0;

  ret = lsm6dsv16x_read_reg(ctx, LSM6DSV16X_CTRL4, (uint8_t *)&ctrl4, 1);

  if (ret == 0)
  {
    ctrl4.int2_in_lh = (uint8_t)val & 0x1U;
    ret = lsm6dsv16x_write_reg(ctx, LSM6DSV16X_CTRL4, (uint8_t *)&ctrl4, 1);
  }

  return ret;
}


int32_t lsm6dsv16x_den_polarity_get(const stmdev_ctx_t *ctx,
                                    lsm6dsv16x_den_polarity_t *val)
{
  lsm6dsv16x_ctrl4_t ctrl4 = {0};
  int32_t ret = 0;

  ret = lsm6dsv16x_read_reg(ctx, LSM6DSV16X_CTRL4, (uint8_t *)&ctrl4, 1);
  if (ret != 0)
  {
    return ret;
  }

  switch (ctrl4.int2_in_lh)
  {
    case 0x00:
      *val = LSM6DSV16X_DEN_ACT_LOW;
      break;

    case 0x01:
      *val = LSM6DSV16X_DEN_ACT_HIGH;
      break;

    default:
      *val = LSM6DSV16X_DEN_ACT_LOW;
      break;
  }

  return ret;
}


int32_t lsm6dsv16x_den_conf_set(const stmdev_ctx_t *ctx, lsm6dsv16x_den_conf_t val)
{
  lsm6dsv16x_den_t den = {0};
  int32_t ret = 0;

  ret = lsm6dsv16x_read_reg(ctx, LSM6DSV16X_DEN, (uint8_t *)&den, 1);
  if (ret != 0)
  {
    return ret;
  }

  den.den_z = val.den_z;
  den.den_y = val.den_y;
  den.den_x = val.den_x;

  den.lvl2_en = (uint8_t)val.mode & 0x1U;
  den.lvl1_en = ((uint8_t)val.mode & 0x2U) >> 1;

  if (val.stamp_in_gy_data == PROPERTY_ENABLE && val.stamp_in_xl_data == PROPERTY_ENABLE)
  {
    den.den_xl_g = PROPERTY_DISABLE;
    den.den_xl_en = PROPERTY_ENABLE;
  }
  else if (val.stamp_in_gy_data == PROPERTY_ENABLE && val.stamp_in_xl_data == PROPERTY_DISABLE)
  {
    den.den_xl_g = PROPERTY_DISABLE;
    den.den_xl_en = PROPERTY_DISABLE;
  }
  else if (val.stamp_in_gy_data == PROPERTY_DISABLE && val.stamp_in_xl_data == PROPERTY_ENABLE)
  {
    den.den_xl_g = PROPERTY_ENABLE;
    den.den_xl_en = PROPERTY_DISABLE;
  }
  else
  {
    den.den_xl_g = PROPERTY_DISABLE;
    den.den_xl_en = PROPERTY_DISABLE;
    den.den_z = PROPERTY_DISABLE;
    den.den_y = PROPERTY_DISABLE;
    den.den_x = PROPERTY_DISABLE;
    den.lvl2_en = PROPERTY_DISABLE;
    den.lvl1_en = PROPERTY_DISABLE;
  }

  ret = lsm6dsv16x_write_reg(ctx, LSM6DSV16X_DEN, (uint8_t *)&den, 1);

  return ret;
}


int32_t lsm6dsv16x_den_conf_get(const stmdev_ctx_t *ctx, lsm6dsv16x_den_conf_t *val)
{
  lsm6dsv16x_den_t den = {0};
  int32_t ret = 0;

  ret = lsm6dsv16x_read_reg(ctx, LSM6DSV16X_DEN, (uint8_t *)&den, 1);
  if (ret != 0)
  {
    return ret;
  }

  val->den_z = den.den_z;
  val->den_y = den.den_y;
  val->den_x = den.den_x;

  if ((den.den_x | den.den_y | den.den_z) == PROPERTY_ENABLE)
  {
    if (den.den_xl_g == PROPERTY_DISABLE && den.den_xl_en == PROPERTY_ENABLE)
    {
      val->stamp_in_gy_data = PROPERTY_ENABLE;
      val->stamp_in_xl_data = PROPERTY_ENABLE;
    }
    else if (den.den_xl_g == PROPERTY_DISABLE && den.den_xl_en == PROPERTY_DISABLE)
    {
      val->stamp_in_gy_data = PROPERTY_ENABLE;
      val->stamp_in_xl_data = PROPERTY_DISABLE;
    }
    else // ( (den.den_xl_g & !den.den_xl_en) == PROPERTY_ENABLE )
    {
      val->stamp_in_gy_data = PROPERTY_DISABLE;
      val->stamp_in_xl_data = PROPERTY_ENABLE;
    }
  }
  else
  {
    val->stamp_in_gy_data = PROPERTY_DISABLE;
    val->stamp_in_xl_data = PROPERTY_DISABLE;
  }

  switch ((den.lvl1_en << 1) + den.lvl2_en)
  {
    case 0x02:
      val->mode = LSM6DSV16X_LEVEL_TRIGGER;
      break;

    case 0x03:
      val->mode = LSM6DSV16X_LEVEL_LATCHED;
      break;

    // 0x00 value and everything else
    default:
      val->mode = LSM6DSV16X_DEN_NOT_DEFINED;
      break;
  }

  return ret;
}


int32_t lsm6dsv16x_eis_gy_full_scale_set(const stmdev_ctx_t *ctx,
                                         lsm6dsv16x_eis_gy_full_scale_t val)
{
  lsm6dsv16x_ctrl_eis_t ctrl_eis = {0};
  int32_t ret = 0;

  ret = lsm6dsv16x_read_reg(ctx, LSM6DSV16X_CTRL_EIS, (uint8_t *)&ctrl_eis, 1);

  if (ret == 0)
  {
    ctrl_eis.fs_g_eis = (uint8_t)val & 0x7U;
    ret = lsm6dsv16x_write_reg(ctx, LSM6DSV16X_CTRL_EIS, (uint8_t *)&ctrl_eis, 1);
  }

  return ret;
}


int32_t lsm6dsv16x_eis_gy_full_scale_get(const stmdev_ctx_t *ctx,
                                         lsm6dsv16x_eis_gy_full_scale_t *val)
{
  lsm6dsv16x_ctrl_eis_t ctrl_eis = {0};
  int32_t ret = 0;

  ret = lsm6dsv16x_read_reg(ctx, LSM6DSV16X_CTRL_EIS, (uint8_t *)&ctrl_eis, 1);
  if (ret != 0)
  {
    return ret;
  }

  switch (ctrl_eis.fs_g_eis)
  {
    case 0x00:
      *val = LSM6DSV16X_EIS_125dps;
      break;

    case 0x01:
      *val = LSM6DSV16X_EIS_250dps;
      break;

    case 0x02:
      *val = LSM6DSV16X_EIS_500dps;
      break;

    case 0x03:
      *val = LSM6DSV16X_EIS_1000dps;
      break;

    case 0x04:
      *val = LSM6DSV16X_EIS_2000dps;
      break;

    default:
      *val = LSM6DSV16X_EIS_125dps;
      break;
  }
  return ret;
}


int32_t lsm6dsv16x_eis_gy_on_spi2_set(const stmdev_ctx_t *ctx, uint8_t val)
{
  lsm6dsv16x_ctrl_eis_t ctrl_eis = {0};
  int32_t ret = 0;

  ret = lsm6dsv16x_read_reg(ctx, LSM6DSV16X_CTRL_EIS, (uint8_t *)&ctrl_eis, 1);

  if (ret == 0)
  {
    ctrl_eis.g_eis_on_g_ois_out_reg = val;
    ret = lsm6dsv16x_write_reg(ctx, LSM6DSV16X_CTRL_EIS, (uint8_t *)&ctrl_eis, 1);
  }

  return ret;
}

int32_t lsm6dsv16x_eis_gy_on_spi2_get(const stmdev_ctx_t *ctx, uint8_t *val)
{
  lsm6dsv16x_ctrl_eis_t ctrl_eis = {0};
  int32_t ret = 0;

  ret = lsm6dsv16x_read_reg(ctx, LSM6DSV16X_CTRL_EIS, (uint8_t *)&ctrl_eis, 1);
  if (ret != 0)
  {
    return ret;
  }

  *val = ctrl_eis.g_eis_on_g_ois_out_reg;

  return ret;
}


int32_t lsm6dsv16x_gy_eis_data_rate_set(const stmdev_ctx_t *ctx,
                                        lsm6dsv16x_gy_eis_data_rate_t val)
{
  lsm6dsv16x_ctrl_eis_t ctrl_eis = {0};
  int32_t ret = 0;

  ret = lsm6dsv16x_read_reg(ctx, LSM6DSV16X_CTRL_EIS, (uint8_t *)&ctrl_eis, 1);

  if (ret == 0)
  {
    ctrl_eis.odr_g_eis = (uint8_t)val & 0x03U;
    ret = lsm6dsv16x_write_reg(ctx, LSM6DSV16X_CTRL_EIS, (uint8_t *)&ctrl_eis, 1);
  }

  return ret;
}


int32_t lsm6dsv16x_gy_eis_data_rate_get(const stmdev_ctx_t *ctx,
                                        lsm6dsv16x_gy_eis_data_rate_t *val)
{
  lsm6dsv16x_ctrl_eis_t ctrl_eis = {0};
  int32_t ret = 0;

  ret = lsm6dsv16x_read_reg(ctx, LSM6DSV16X_CTRL_EIS, (uint8_t *)&ctrl_eis, 1);
  if (ret != 0)
  {
    return ret;
  }

  switch (ctrl_eis.odr_g_eis)
  {
    case 0x00:
      *val = LSM6DSV16X_EIS_ODR_OFF;
      break;

    case 0x01:
      *val = LSM6DSV16X_EIS_1920Hz;
      break;

    case 0x02:
      *val = LSM6DSV16X_EIS_960Hz;
      break;

    default:
      *val = LSM6DSV16X_EIS_1920Hz;
      break;
  }

  return ret;
}


int32_t lsm6dsv16x_fifo_watermark_set(const stmdev_ctx_t *ctx, uint8_t val)
{
  lsm6dsv16x_fifo_ctrl1_t fifo_ctrl1 = {0};
  int32_t ret = 0;

  fifo_ctrl1.wtm = val;
  ret = lsm6dsv16x_write_reg(ctx, LSM6DSV16X_FIFO_CTRL1, (uint8_t *)&fifo_ctrl1, 1);

  return ret;
}

int32_t lsm6dsv16x_fifo_watermark_get(const stmdev_ctx_t *ctx, uint8_t *val)
{
  lsm6dsv16x_fifo_ctrl1_t fifo_ctrl1 = {0};
  int32_t ret = 0;

  ret = lsm6dsv16x_read_reg(ctx, LSM6DSV16X_FIFO_CTRL1, (uint8_t *)&fifo_ctrl1, 1);
  if (ret != 0)
  {
    return ret;
  }

  *val = fifo_ctrl1.wtm;

  return ret;
}


int32_t lsm6dsv16x_fifo_xl_dual_fsm_batch_set(const stmdev_ctx_t *ctx, uint8_t val)
{
  lsm6dsv16x_fifo_ctrl2_t fifo_ctrl2 = {0};
  int32_t ret = 0;

  ret = lsm6dsv16x_read_reg(ctx, LSM6DSV16X_FIFO_CTRL2, (uint8_t *)&fifo_ctrl2, 1);
  if (ret == 0)
  {
    fifo_ctrl2.xl_dualc_batch_from_fsm = val;
    ret = lsm6dsv16x_write_reg(ctx, LSM6DSV16X_FIFO_CTRL2, (uint8_t *)&fifo_ctrl2, 1);
  }

  return ret;
}

int32_t lsm6dsv16x_fifo_xl_dual_fsm_batch_get(const stmdev_ctx_t *ctx, uint8_t *val)
{
  lsm6dsv16x_fifo_ctrl2_t fifo_ctrl2 = {0};
  int32_t ret = 0;

  ret = lsm6dsv16x_read_reg(ctx, LSM6DSV16X_FIFO_CTRL2, (uint8_t *)&fifo_ctrl2, 1);
  if (ret != 0)
  {
    return ret;
  }

  *val = fifo_ctrl2.xl_dualc_batch_from_fsm;

  return ret;
}


int32_t lsm6dsv16x_fifo_compress_algo_set(const stmdev_ctx_t *ctx,
                                          lsm6dsv16x_fifo_compress_algo_t val)
{
  lsm6dsv16x_fifo_ctrl2_t fifo_ctrl2 = {0};
  int32_t ret = 0;

  ret = lsm6dsv16x_read_reg(ctx, LSM6DSV16X_FIFO_CTRL2, (uint8_t *)&fifo_ctrl2, 1);
  if (ret == 0)
  {
    fifo_ctrl2.uncompr_rate = (uint8_t)val & 0x03U;
    ret = lsm6dsv16x_write_reg(ctx, LSM6DSV16X_FIFO_CTRL2, (uint8_t *)&fifo_ctrl2, 1);
  }

  return ret;
}


int32_t lsm6dsv16x_fifo_compress_algo_get(const stmdev_ctx_t *ctx,
                                          lsm6dsv16x_fifo_compress_algo_t *val)
{
  lsm6dsv16x_fifo_ctrl2_t fifo_ctrl2 = {0};
  int32_t ret = 0;

  ret = lsm6dsv16x_read_reg(ctx, LSM6DSV16X_FIFO_CTRL2, (uint8_t *)&fifo_ctrl2, 1);
  if (ret != 0)
  {
    return ret;
  }

  switch (fifo_ctrl2.uncompr_rate)
  {
    case 0x00:
      *val = LSM6DSV16X_CMP_DISABLE;
      break;

    case 0x01:
      *val = LSM6DSV16X_CMP_8_TO_1;
      break;

    case 0x02:
      *val = LSM6DSV16X_CMP_16_TO_1;
      break;

    case 0x03:
      *val = LSM6DSV16X_CMP_32_TO_1;
      break;

    default:
      *val = LSM6DSV16X_CMP_DISABLE;
      break;
  }
  return ret;
}


int32_t lsm6dsv16x_fifo_virtual_sens_odr_chg_set(const stmdev_ctx_t *ctx, uint8_t val)
{
  lsm6dsv16x_fifo_ctrl2_t fifo_ctrl2 = {0};
  int32_t ret = 0;

  ret = lsm6dsv16x_read_reg(ctx, LSM6DSV16X_FIFO_CTRL2, (uint8_t *)&fifo_ctrl2, 1);
  if (ret == 0)
  {
    fifo_ctrl2.odr_chg_en = val;
    ret = lsm6dsv16x_write_reg(ctx, LSM6DSV16X_FIFO_CTRL2, (uint8_t *)&fifo_ctrl2, 1);
  }

  return ret;
}


int32_t lsm6dsv16x_fifo_virtual_sens_odr_chg_get(const stmdev_ctx_t *ctx,
                                                 uint8_t *val)
{
  lsm6dsv16x_fifo_ctrl2_t fifo_ctrl2 = {0};
  int32_t ret = 0;

  ret = lsm6dsv16x_read_reg(ctx, LSM6DSV16X_FIFO_CTRL2, (uint8_t *)&fifo_ctrl2, 1);
  if (ret != 0)
  {
    return ret;
  }

  *val = fifo_ctrl2.odr_chg_en;

  return ret;
}


int32_t lsm6dsv16x_fifo_compress_algo_real_time_set(const stmdev_ctx_t *ctx,
                                                    uint8_t val)
{
  lsm6dsv16x_emb_func_en_b_t emb_func_en_b = {0};
  lsm6dsv16x_fifo_ctrl2_t fifo_ctrl2 = {0};

  int32_t ret = 0;

  ret = lsm6dsv16x_read_reg(ctx, LSM6DSV16X_FIFO_CTRL2, (uint8_t *)&fifo_ctrl2, 1);
  if (ret != 0)
  {
    return ret;
  }
  fifo_ctrl2.fifo_compr_rt_en = val;
  ret += lsm6dsv16x_write_reg(ctx, LSM6DSV16X_FIFO_CTRL2, (uint8_t *)&fifo_ctrl2, 1);
  if (ret != 0)
  {
    return ret;
  }

  ret = lsm6dsv16x_mem_bank_set(ctx, LSM6DSV16X_EMBED_FUNC_MEM_BANK);
  if (ret != 0)
  {
    return ret;
  }

  ret = lsm6dsv16x_read_reg(ctx, LSM6DSV16X_EMB_FUNC_EN_B, (uint8_t *)&emb_func_en_b, 1);
  if (ret == 0)
  {
    emb_func_en_b.fifo_compr_en = val;
    ret += lsm6dsv16x_write_reg(ctx, LSM6DSV16X_EMB_FUNC_EN_B, (uint8_t *)&emb_func_en_b, 1);
  }
  ret += lsm6dsv16x_mem_bank_set(ctx, LSM6DSV16X_MAIN_MEM_BANK);

  return ret;
}


int32_t lsm6dsv16x_fifo_compress_algo_real_time_get(const stmdev_ctx_t *ctx,
                                                    uint8_t *val)
{
  lsm6dsv16x_fifo_ctrl2_t fifo_ctrl2 = {0};
  int32_t ret = 0;

  ret = lsm6dsv16x_read_reg(ctx, LSM6DSV16X_FIFO_CTRL2, (uint8_t *)&fifo_ctrl2, 1);
  if (ret != 0)
  {
    return ret;
  }

  *val = fifo_ctrl2.fifo_compr_rt_en;

  return ret;
}


int32_t lsm6dsv16x_fifo_stop_on_wtm_set(const stmdev_ctx_t *ctx, lsm6dsv16x_fifo_event_t val)
{
  lsm6dsv16x_fifo_ctrl2_t fifo_ctrl2 = {0};
  int32_t ret = 0;

  ret = lsm6dsv16x_read_reg(ctx, LSM6DSV16X_FIFO_CTRL2, (uint8_t *)&fifo_ctrl2, 1);
  if (ret == 0)
  {
    fifo_ctrl2.stop_on_wtm = (val == LSM6DSV16X_FIFO_EV_WTM) ? 1U : 0U;
    ret = lsm6dsv16x_write_reg(ctx, LSM6DSV16X_FIFO_CTRL2, (uint8_t *)&fifo_ctrl2, 1);
  }

  return ret;
}


int32_t lsm6dsv16x_fifo_stop_on_wtm_get(const stmdev_ctx_t *ctx, lsm6dsv16x_fifo_event_t *val)
{
  lsm6dsv16x_fifo_ctrl2_t fifo_ctrl2 = {0};
  int32_t ret = 0;

  ret = lsm6dsv16x_read_reg(ctx, LSM6DSV16X_FIFO_CTRL2, (uint8_t *)&fifo_ctrl2, 1);
  if (ret == 0)
  {
    *val = (fifo_ctrl2.stop_on_wtm == 1u) ? LSM6DSV16X_FIFO_EV_WTM : LSM6DSV16X_FIFO_EV_FULL;
  }

  return ret;
}


int32_t lsm6dsv16x_fifo_xl_batch_set(const stmdev_ctx_t *ctx,
                                     lsm6dsv16x_fifo_xl_batch_t val)
{
  lsm6dsv16x_fifo_ctrl3_t fifo_ctrl3 = {0};
  int32_t ret = 0;

  ret = lsm6dsv16x_read_reg(ctx, LSM6DSV16X_FIFO_CTRL3, (uint8_t *)&fifo_ctrl3, 1);
  if (ret == 0)
  {
    fifo_ctrl3.bdr_xl = (uint8_t)val & 0xFu;
    ret = lsm6dsv16x_write_reg(ctx, LSM6DSV16X_FIFO_CTRL3, (uint8_t *)&fifo_ctrl3, 1);
  }

  return ret;
}

int32_t lsm6dsv16x_fifo_xl_batch_get(const stmdev_ctx_t *ctx,
                                     lsm6dsv16x_fifo_xl_batch_t *val)
{
  lsm6dsv16x_fifo_ctrl3_t fifo_ctrl3 = {0};
  int32_t ret = 0;

  ret = lsm6dsv16x_read_reg(ctx, LSM6DSV16X_FIFO_CTRL3, (uint8_t *)&fifo_ctrl3, 1);
  if (ret != 0)
  {
    return ret;
  }

  switch (fifo_ctrl3.bdr_xl)
  {
    case 0x00:
      *val = LSM6DSV16X_XL_NOT_BATCHED;
      break;

    case 0x01:
      *val = LSM6DSV16X_XL_BATCHED_AT_1Hz875;
      break;

    case 0x02:
      *val = LSM6DSV16X_XL_BATCHED_AT_7Hz5;
      break;

    case 0x03:
      *val = LSM6DSV16X_XL_BATCHED_AT_15Hz;
      break;

    case 0x04:
      *val = LSM6DSV16X_XL_BATCHED_AT_30Hz;
      break;

    case 0x05:
      *val = LSM6DSV16X_XL_BATCHED_AT_60Hz;
      break;

    case 0x06:
      *val = LSM6DSV16X_XL_BATCHED_AT_120Hz;
      break;

    case 0x07:
      *val = LSM6DSV16X_XL_BATCHED_AT_240Hz;
      break;

    case 0x08:
      *val = LSM6DSV16X_XL_BATCHED_AT_480Hz;
      break;

    case 0x09:
      *val = LSM6DSV16X_XL_BATCHED_AT_960Hz;
      break;

    case 0x0A:
      *val = LSM6DSV16X_XL_BATCHED_AT_1920Hz;
      break;

    case 0x0B:
      *val = LSM6DSV16X_XL_BATCHED_AT_3840Hz;
      break;

    case 0x0C:
      *val = LSM6DSV16X_XL_BATCHED_AT_7680Hz;
      break;

    default:
      *val = LSM6DSV16X_XL_NOT_BATCHED;
      break;
  }

  return ret;
}


int32_t lsm6dsv16x_fifo_gy_batch_set(const stmdev_ctx_t *ctx,
                                     lsm6dsv16x_fifo_gy_batch_t val)
{
  lsm6dsv16x_fifo_ctrl3_t fifo_ctrl3 = {0};
  int32_t ret = 0;

  ret = lsm6dsv16x_read_reg(ctx, LSM6DSV16X_FIFO_CTRL3, (uint8_t *)&fifo_ctrl3, 1);
  if (ret == 0)
  {
    fifo_ctrl3.bdr_gy = (uint8_t)val & 0x0Fu;
    ret = lsm6dsv16x_write_reg(ctx, LSM6DSV16X_FIFO_CTRL3, (uint8_t *)&fifo_ctrl3, 1);
  }

  return ret;
}

int32_t lsm6dsv16x_fifo_gy_batch_get(const stmdev_ctx_t *ctx,
                                     lsm6dsv16x_fifo_gy_batch_t *val)
{
  lsm6dsv16x_fifo_ctrl3_t fifo_ctrl3 = {0};
  int32_t ret = 0;

  ret = lsm6dsv16x_read_reg(ctx, LSM6DSV16X_FIFO_CTRL3, (uint8_t *)&fifo_ctrl3, 1);
  if (ret != 0)
  {
    return ret;
  }

  switch (fifo_ctrl3.bdr_gy)
  {
    case 0x00:
      *val = LSM6DSV16X_GY_NOT_BATCHED;
      break;

    case 0x01:
      *val = LSM6DSV16X_GY_BATCHED_AT_1Hz875;
      break;

    case 0x02:
      *val = LSM6DSV16X_GY_BATCHED_AT_7Hz5;
      break;

    case 0x03:
      *val = LSM6DSV16X_GY_BATCHED_AT_15Hz;
      break;

    case 0x04:
      *val = LSM6DSV16X_GY_BATCHED_AT_30Hz;
      break;

    case 0x05:
      *val = LSM6DSV16X_GY_BATCHED_AT_60Hz;
      break;

    case 0x06:
      *val = LSM6DSV16X_GY_BATCHED_AT_120Hz;
      break;

    case 0x07:
      *val = LSM6DSV16X_GY_BATCHED_AT_240Hz;
      break;

    case 0x08:
      *val = LSM6DSV16X_GY_BATCHED_AT_480Hz;
      break;

    case 0x09:
      *val = LSM6DSV16X_GY_BATCHED_AT_960Hz;
      break;

    case 0x0A:
      *val = LSM6DSV16X_GY_BATCHED_AT_1920Hz;
      break;

    case 0x0B:
      *val = LSM6DSV16X_GY_BATCHED_AT_3840Hz;
      break;

    case 0x0C:
      *val = LSM6DSV16X_GY_BATCHED_AT_7680Hz;
      break;

    default:
      *val = LSM6DSV16X_GY_NOT_BATCHED;
      break;
  }
  return ret;
}



int32_t lsm6dsv16x_fifo_mode_set(const stmdev_ctx_t *ctx, lsm6dsv16x_fifo_mode_t val)
{
  lsm6dsv16x_fifo_ctrl4_t fifo_ctrl4 = {0};
  int32_t ret = 0;

  ret = lsm6dsv16x_read_reg(ctx, LSM6DSV16X_FIFO_CTRL4, (uint8_t *)&fifo_ctrl4, 1);
  if (ret == 0)
  {
    fifo_ctrl4.fifo_mode = (uint8_t)val & 0x07U;
    ret = lsm6dsv16x_write_reg(ctx, LSM6DSV16X_FIFO_CTRL4, (uint8_t *)&fifo_ctrl4, 1);
  }

  return ret;
}


int32_t lsm6dsv16x_fifo_mode_get(const stmdev_ctx_t *ctx, lsm6dsv16x_fifo_mode_t *val)
{
  lsm6dsv16x_fifo_ctrl4_t fifo_ctrl4 = {0};
  int32_t ret = 0;

  ret = lsm6dsv16x_read_reg(ctx, LSM6DSV16X_FIFO_CTRL4, (uint8_t *)&fifo_ctrl4, 1);
  if (ret != 0)
  {
    return ret;
  }

  switch (fifo_ctrl4.fifo_mode)
  {
    case 0x00:
      *val = LSM6DSV16X_BYPASS_MODE;
      break;

    case 0x01:
      *val = LSM6DSV16X_FIFO_MODE;
      break;

    case 0x02:
      *val = LSM6DSV16X_STREAM_WTM_TO_FULL_MODE;
      break;

    case 0x03:
      *val = LSM6DSV16X_STREAM_TO_FIFO_MODE;
      break;

    case 0x04:
      *val = LSM6DSV16X_BYPASS_TO_STREAM_MODE;
      break;

    case 0x06:
      *val = LSM6DSV16X_STREAM_MODE;
      break;

    case 0x07:
      *val = LSM6DSV16X_BYPASS_TO_FIFO_MODE;
      break;

    default:
      *val = LSM6DSV16X_BYPASS_MODE;
      break;
  }
  return ret;
}


int32_t lsm6dsv16x_fifo_gy_eis_batch_set(const stmdev_ctx_t *ctx, uint8_t val)
{
  lsm6dsv16x_fifo_ctrl4_t fifo_ctrl4 = {0};
  int32_t ret = {0};

  ret = lsm6dsv16x_read_reg(ctx, LSM6DSV16X_FIFO_CTRL4, (uint8_t *)&fifo_ctrl4, 1);
  if (ret == 0)
  {
    fifo_ctrl4.g_eis_fifo_en = val;
    ret = lsm6dsv16x_write_reg(ctx, LSM6DSV16X_FIFO_CTRL4, (uint8_t *)&fifo_ctrl4, 1);
  }

  return ret;
}


int32_t lsm6dsv16x_fifo_gy_eis_batch_get(const stmdev_ctx_t *ctx, uint8_t *val)
{
  lsm6dsv16x_fifo_ctrl4_t fifo_ctrl4 = {0};
  int32_t ret = 0;

  ret = lsm6dsv16x_read_reg(ctx, LSM6DSV16X_FIFO_CTRL4, (uint8_t *)&fifo_ctrl4, 1);
  if (ret != 0)
  {
    return ret;
  }

  *val = fifo_ctrl4.g_eis_fifo_en;

  return ret;
}

int32_t lsm6dsv16x_fifo_temp_batch_set(const stmdev_ctx_t *ctx,
                                       lsm6dsv16x_fifo_temp_batch_t val)
{
  lsm6dsv16x_fifo_ctrl4_t fifo_ctrl4 = {0};
  int32_t ret = 0;

  ret = lsm6dsv16x_read_reg(ctx, LSM6DSV16X_FIFO_CTRL4, (uint8_t *)&fifo_ctrl4, 1);
  if (ret == 0)
  {
    fifo_ctrl4.odr_t_batch = (uint8_t)val & 0x03U;
    ret = lsm6dsv16x_write_reg(ctx, LSM6DSV16X_FIFO_CTRL4, (uint8_t *)&fifo_ctrl4, 1);
  }

  return ret;
}


int32_t lsm6dsv16x_fifo_temp_batch_get(const stmdev_ctx_t *ctx,
                                       lsm6dsv16x_fifo_temp_batch_t *val)
{
  lsm6dsv16x_fifo_ctrl4_t fifo_ctrl4 = {0};
  int32_t ret = 0;

  ret = lsm6dsv16x_read_reg(ctx, LSM6DSV16X_FIFO_CTRL4, (uint8_t *)&fifo_ctrl4, 1);
  if (ret != 0)
  {
    return ret;
  }

  switch (fifo_ctrl4.odr_t_batch)
  {
    case 0x00:
      *val = LSM6DSV16X_TEMP_NOT_BATCHED;
      break;

    case 0x01:
      *val = LSM6DSV16X_TEMP_BATCHED_AT_1Hz875;
      break;

    case 0x02:
      *val = LSM6DSV16X_TEMP_BATCHED_AT_15Hz;
      break;

    case 0x03:
      *val = LSM6DSV16X_TEMP_BATCHED_AT_60Hz;
      break;

    default:
      *val = LSM6DSV16X_TEMP_NOT_BATCHED;
      break;
  }
  return ret;
}


int32_t lsm6dsv16x_fifo_timestamp_batch_set(const stmdev_ctx_t *ctx,
                                            lsm6dsv16x_fifo_timestamp_batch_t val)
{
  lsm6dsv16x_fifo_ctrl4_t fifo_ctrl4 = {0};
  int32_t ret = 0;

  ret = lsm6dsv16x_read_reg(ctx, LSM6DSV16X_FIFO_CTRL4, (uint8_t *)&fifo_ctrl4, 1);
  if (ret == 0)
  {
    fifo_ctrl4.dec_ts_batch = (uint8_t)val & 0x03U;
    ret = lsm6dsv16x_write_reg(ctx, LSM6DSV16X_FIFO_CTRL4, (uint8_t *)&fifo_ctrl4, 1);
  }

  return ret;
}


int32_t lsm6dsv16x_fifo_timestamp_batch_get(const stmdev_ctx_t *ctx,
                                            lsm6dsv16x_fifo_timestamp_batch_t *val)
{
  lsm6dsv16x_fifo_ctrl4_t fifo_ctrl4 = {0};
  int32_t ret = 0;

  ret = lsm6dsv16x_read_reg(ctx, LSM6DSV16X_FIFO_CTRL4, (uint8_t *)&fifo_ctrl4, 1);
  if (ret != 0)
  {
    return ret;
  }

  switch (fifo_ctrl4.dec_ts_batch)
  {
    case 0x00:
      *val = LSM6DSV16X_TMSTMP_NOT_BATCHED;
      break;

    case 0x01:
      *val = LSM6DSV16X_TMSTMP_DEC_1;
      break;

    case 0x02:
      *val = LSM6DSV16X_TMSTMP_DEC_8;
      break;

    case 0x03:
      *val = LSM6DSV16X_TMSTMP_DEC_32;
      break;

    default:
      *val = LSM6DSV16X_TMSTMP_NOT_BATCHED;
      break;
  }

  return ret;
}


int32_t lsm6dsv16x_fifo_batch_counter_threshold_set(const stmdev_ctx_t *ctx,
                                                    uint16_t val)
{
  lsm6dsv16x_counter_bdr_reg1_t counter_bdr_reg1 = {0};
  lsm6dsv16x_counter_bdr_reg2_t counter_bdr_reg2 = {0};
  int32_t ret = 0;

  ret = lsm6dsv16x_read_reg(ctx, LSM6DSV16X_COUNTER_BDR_REG1, (uint8_t *)&counter_bdr_reg1, 1);

  if (ret == 0)
  {
    counter_bdr_reg2.cnt_bdr_th = (uint8_t)val & 0xFFU;
    counter_bdr_reg1.cnt_bdr_th = (uint8_t)(val >> 8) & 0x3U;
    ret = lsm6dsv16x_write_reg(ctx, LSM6DSV16X_COUNTER_BDR_REG1, (uint8_t *)&counter_bdr_reg1, 1);
    ret += lsm6dsv16x_write_reg(ctx, LSM6DSV16X_COUNTER_BDR_REG2, (uint8_t *)&counter_bdr_reg2, 1);
  }

  return ret;
}


int32_t lsm6dsv16x_fifo_batch_counter_threshold_get(const stmdev_ctx_t *ctx,
                                                    uint16_t *val)
{
  uint8_t buff[2] = {0};
  int32_t ret = {0};

  ret = lsm6dsv16x_read_reg(ctx, LSM6DSV16X_COUNTER_BDR_REG1, &buff[0], 2);
  if (ret != 0)
  {
    return ret;
  }

  *val = (uint16_t)buff[0] & 0x3U;
  *val = (*val * 256U) + (uint16_t)buff[1];

  return ret;
}

int32_t lsm6dsv16x_fifo_batch_cnt_event_set(const stmdev_ctx_t *ctx,
                                            lsm6dsv16x_fifo_batch_cnt_event_t val)
{
  lsm6dsv16x_counter_bdr_reg1_t counter_bdr_reg1 = {0};
  int32_t ret = 0;

  ret = lsm6dsv16x_read_reg(ctx, LSM6DSV16X_COUNTER_BDR_REG1, (uint8_t *)&counter_bdr_reg1, 1);
  if (ret == 0)
  {
    counter_bdr_reg1.trig_counter_bdr = (uint8_t)val & 0x03U;
    ret = lsm6dsv16x_write_reg(ctx, LSM6DSV16X_COUNTER_BDR_REG1, (uint8_t *)&counter_bdr_reg1, 1);
  }

  return ret;
}


int32_t lsm6dsv16x_fifo_batch_cnt_event_get(const stmdev_ctx_t *ctx,
                                            lsm6dsv16x_fifo_batch_cnt_event_t *val)
{
  lsm6dsv16x_counter_bdr_reg1_t counter_bdr_reg1 = {0};
  int32_t ret = 0;

  ret = lsm6dsv16x_read_reg(ctx, LSM6DSV16X_COUNTER_BDR_REG1, (uint8_t *)&counter_bdr_reg1, 1);
  if (ret != 0)
  {
    return ret;
  }

  switch (counter_bdr_reg1.trig_counter_bdr)
  {
    case 0x00:
      *val = LSM6DSV16X_XL_BATCH_EVENT;
      break;

    case 0x01:
      *val = LSM6DSV16X_GY_BATCH_EVENT;
      break;

    case 0x02:
      *val = LSM6DSV16X_GY_EIS_BATCH_EVENT;
      break;

    default:
      *val = LSM6DSV16X_XL_BATCH_EVENT;
      break;
  }

  return ret;
}

int32_t lsm6dsv16x_fifo_xl_dual_channel_batch_set(const stmdev_ctx_t *ctx, uint8_t val)
{
  lsm6dsv16x_emb_func_cfg_t emb_func_cfg = {0};
  int32_t ret = 0;

  ret = lsm6dsv16x_read_reg(ctx, LSM6DSV16X_EMB_FUNC_CFG, (uint8_t *)&emb_func_cfg, 1);
  if (ret != 0)
  {
    return ret;
  }

  emb_func_cfg.xl_dualc_batch_from_if = val;
  ret += lsm6dsv16x_write_reg(ctx, LSM6DSV16X_EMB_FUNC_CFG, (uint8_t *)&emb_func_cfg, 1);

  return ret;
}

int32_t lsm6dsv16x_fifo_xl_dual_channel_batch_get(const stmdev_ctx_t *ctx, uint8_t *val)
{
  lsm6dsv16x_emb_func_cfg_t emb_func_cfg = {0};
  int32_t ret = 0;

  ret = lsm6dsv16x_read_reg(ctx, LSM6DSV16X_EMB_FUNC_CFG, (uint8_t *)&emb_func_cfg, 1);
  if (ret == 0)
  {
    *val = emb_func_cfg.xl_dualc_batch_from_if;
  }

  return ret;
}

int32_t lsm6dsv16x_fifo_status_get(const stmdev_ctx_t *ctx,
                                   lsm6dsv16x_fifo_status_t *val)
{
  uint8_t buff[2] = {0};
  lsm6dsv16x_fifo_status2_t status = {0};
  int32_t ret = 0;

  ret = lsm6dsv16x_read_reg(ctx, LSM6DSV16X_FIFO_STATUS1, (uint8_t *)&buff[0], 2);
  if (ret != 0)
  {
    return ret;
  }

  bytecpy((uint8_t *)&status, &buff[1]);

  val->fifo_bdr = status.counter_bdr_ia;
  val->fifo_ovr = status.fifo_ovr_ia;
  val->fifo_full = status.fifo_full_ia;
  val->fifo_th = status.fifo_wtm_ia;

  val->fifo_level = (uint16_t)buff[1] & 0x01U;
  val->fifo_level = (val->fifo_level * 256U) + buff[0];

  return ret;
}


int32_t lsm6dsv16x_fifo_out_raw_get(const stmdev_ctx_t *ctx,
                                    lsm6dsv16x_fifo_out_raw_t *val)
{
  lsm6dsv16x_fifo_data_out_tag_t fifo_data_out_tag = {0};
  uint8_t buff[7] = {0};
  int32_t ret = 0;

  ret = lsm6dsv16x_read_reg(ctx, LSM6DSV16X_FIFO_DATA_OUT_TAG, buff, 7);
  if (ret != 0)
  {
    return ret;
  }

  bytecpy((uint8_t *)&fifo_data_out_tag, &buff[0]);

  switch (fifo_data_out_tag.tag_sensor)
  {
    case 0x00:
      val->tag = (uint8_t)LSM6DSV16X_FIFO_EMPTY;
      break;

    case 0x01:
      val->tag = (uint8_t)LSM6DSV16X_GY_NC_TAG;
      break;

    case 0x02:
      val->tag = (uint8_t)LSM6DSV16X_XL_NC_TAG;
      break;

    case 0x03:
      val->tag = (uint8_t)LSM6DSV16X_TEMPERATURE_TAG;
      break;

    case 0x04:
      val->tag = (uint8_t)LSM6DSV16X_TIMESTAMP_TAG;
      break;

    case 0x05:
      val->tag = (uint8_t)LSM6DSV16X_CFG_CHANGE_TAG;
      break;

    case 0x06:
      val->tag = (uint8_t)LSM6DSV16X_XL_NC_T_2_TAG;
      break;

    case 0x07:
      val->tag = (uint8_t)LSM6DSV16X_XL_NC_T_1_TAG;
      break;

    case 0x08:
      val->tag = (uint8_t)LSM6DSV16X_XL_2XC_TAG;
      break;

    case 0x09:
      val->tag = (uint8_t)LSM6DSV16X_XL_3XC_TAG;
      break;

    case 0x0A:
      val->tag = (uint8_t)LSM6DSV16X_GY_NC_T_2_TAG;
      break;

    case 0x0B:
      val->tag = (uint8_t)LSM6DSV16X_GY_NC_T_1_TAG;
      break;

    case 0x0C:
      val->tag = (uint8_t)LSM6DSV16X_GY_2XC_TAG;
      break;

    case 0x0D:
      val->tag = (uint8_t)LSM6DSV16X_GY_3XC_TAG;
      break;

    case 0x0E:
      val->tag = (uint8_t)LSM6DSV16X_SENSORHUB_SLAVE0_TAG;
      break;

    case 0x0F:
      val->tag = (uint8_t)LSM6DSV16X_SENSORHUB_SLAVE1_TAG;
      break;

    case 0x10:
      val->tag = (uint8_t)LSM6DSV16X_SENSORHUB_SLAVE2_TAG;
      break;

    case 0x11:
      val->tag = (uint8_t)LSM6DSV16X_SENSORHUB_SLAVE3_TAG;
      break;

    case 0x12:
      val->tag = (uint8_t)LSM6DSV16X_STEP_COUNTER_TAG;
      break;

    case 0x13:
      val->tag = (uint8_t)LSM6DSV16X_SFLP_GAME_ROTATION_VECTOR_TAG;
      break;

    case 0x16:
      val->tag = (uint8_t)LSM6DSV16X_SFLP_GYROSCOPE_BIAS_TAG;
      break;

    case 0x17:
      val->tag = (uint8_t)LSM6DSV16X_SFLP_GRAVITY_VECTOR_TAG;
      break;

    case 0x19:
      val->tag = (uint8_t)LSM6DSV16X_SENSORHUB_NACK_TAG;
      break;

    case 0x1A:
      val->tag = (uint8_t)LSM6DSV16X_MLC_RESULT_TAG;
      break;

    case 0x1B:
      val->tag = (uint8_t)LSM6DSV16X_MLC_FILTER;
      break;

    case 0x1C:
      val->tag = (uint8_t)LSM6DSV16X_MLC_FEATURE;
      break;

    case 0x1D:
      val->tag = (uint8_t)LSM6DSV16X_XL_DUAL_CORE;
      break;

    case 0x1E:
      val->tag = (uint8_t)LSM6DSV16X_GY_ENHANCED_EIS;
      break;

    default:
      val->tag = (uint8_t)LSM6DSV16X_FIFO_EMPTY;
      break;
  }

  val->cnt = fifo_data_out_tag.tag_cnt;

  val->data[0] = buff[1];
  val->data[1] = buff[2];
  val->data[2] = buff[3];
  val->data[3] = buff[4];
  val->data[4] = buff[5];
  val->data[5] = buff[6];

  return ret;
}


int32_t lsm6dsv16x_fifo_stpcnt_batch_set(const stmdev_ctx_t *ctx, uint8_t val)
{
  lsm6dsv16x_emb_func_fifo_en_a_t emb_func_fifo_en_a = {0};
  int32_t ret = 0;

  ret = lsm6dsv16x_mem_bank_set(ctx, LSM6DSV16X_EMBED_FUNC_MEM_BANK);
  if (ret != 0)
  {
    return ret;
  }

  ret = lsm6dsv16x_read_reg(ctx, LSM6DSV16X_EMB_FUNC_FIFO_EN_A, (uint8_t *)&emb_func_fifo_en_a, 1);
  if (ret == 0)
  {
    emb_func_fifo_en_a.step_counter_fifo_en = val;
    ret += lsm6dsv16x_write_reg(ctx, LSM6DSV16X_EMB_FUNC_FIFO_EN_A, (uint8_t *)&emb_func_fifo_en_a, 1);
  }

  ret += lsm6dsv16x_mem_bank_set(ctx, LSM6DSV16X_MAIN_MEM_BANK);

  return ret;
}


int32_t lsm6dsv16x_fifo_stpcnt_batch_get(const stmdev_ctx_t *ctx, uint8_t *val)
{
  lsm6dsv16x_emb_func_fifo_en_a_t emb_func_fifo_en_a = {0};
  int32_t ret = 0;

  ret = lsm6dsv16x_mem_bank_set(ctx, LSM6DSV16X_EMBED_FUNC_MEM_BANK);
  if (ret != 0)
  {
    return ret;
  }

  ret += lsm6dsv16x_read_reg(ctx, LSM6DSV16X_EMB_FUNC_FIFO_EN_A, (uint8_t *)&emb_func_fifo_en_a, 1);
  if (ret == 0)
  {
    *val = emb_func_fifo_en_a.step_counter_fifo_en;
  }

  ret += lsm6dsv16x_mem_bank_set(ctx, LSM6DSV16X_MAIN_MEM_BANK);

  return ret;
}

int32_t lsm6dsv16x_fifo_mlc_batch_set(const stmdev_ctx_t *ctx, uint8_t val)
{
  lsm6dsv16x_emb_func_fifo_en_a_t emb_func_fifo_en_a = {0};
  int32_t ret = 0;

  ret = lsm6dsv16x_mem_bank_set(ctx, LSM6DSV16X_EMBED_FUNC_MEM_BANK);
  if (ret != 0)
  {
    return ret;
  }

  ret = lsm6dsv16x_read_reg(ctx, LSM6DSV16X_EMB_FUNC_FIFO_EN_A, (uint8_t *)&emb_func_fifo_en_a, 1);
  if (ret == 0)
  {
    emb_func_fifo_en_a.mlc_fifo_en = val;
    ret += lsm6dsv16x_write_reg(ctx, LSM6DSV16X_EMB_FUNC_FIFO_EN_A, (uint8_t *)&emb_func_fifo_en_a, 1);
  }

  ret += lsm6dsv16x_mem_bank_set(ctx, LSM6DSV16X_MAIN_MEM_BANK);

  return ret;
}


int32_t lsm6dsv16x_fifo_mlc_batch_get(const stmdev_ctx_t *ctx, uint8_t *val)
{
  lsm6dsv16x_emb_func_fifo_en_a_t emb_func_fifo_en_a = {0};
  int32_t ret = 0;

  ret = lsm6dsv16x_mem_bank_set(ctx, LSM6DSV16X_EMBED_FUNC_MEM_BANK);
  if (ret != 0)
  {
    return ret;
  }

  ret = lsm6dsv16x_read_reg(ctx, LSM6DSV16X_EMB_FUNC_FIFO_EN_A, (uint8_t *)&emb_func_fifo_en_a, 1);
  if (ret == 0)
  {
    *val = emb_func_fifo_en_a.mlc_fifo_en;
  }

  ret += lsm6dsv16x_mem_bank_set(ctx, LSM6DSV16X_MAIN_MEM_BANK);

  return ret;
}


int32_t lsm6dsv16x_fifo_mlc_filt_batch_set(const stmdev_ctx_t *ctx, uint8_t val)
{
  lsm6dsv16x_emb_func_fifo_en_b_t emb_func_fifo_en_b = {0};
  int32_t ret = 0;

  ret = lsm6dsv16x_mem_bank_set(ctx, LSM6DSV16X_EMBED_FUNC_MEM_BANK);
  if (ret != 0)
  {
    return ret;
  }

  ret = lsm6dsv16x_read_reg(ctx, LSM6DSV16X_EMB_FUNC_FIFO_EN_B, (uint8_t *)&emb_func_fifo_en_b, 1);
  if (ret == 0)
  {
    emb_func_fifo_en_b.mlc_filter_feature_fifo_en = val;
    ret += lsm6dsv16x_write_reg(ctx, LSM6DSV16X_EMB_FUNC_FIFO_EN_B, (uint8_t *)&emb_func_fifo_en_b, 1);
  }

  ret += lsm6dsv16x_mem_bank_set(ctx, LSM6DSV16X_MAIN_MEM_BANK);

  return ret;
}


int32_t lsm6dsv16x_fifo_mlc_filt_batch_get(const stmdev_ctx_t *ctx, uint8_t *val)
{
  lsm6dsv16x_emb_func_fifo_en_b_t emb_func_fifo_en_b = {0};
  int32_t ret = 0;

  ret = lsm6dsv16x_mem_bank_set(ctx, LSM6DSV16X_EMBED_FUNC_MEM_BANK);
  if (ret != 0)
  {
    return ret;
  }

  ret = lsm6dsv16x_read_reg(ctx, LSM6DSV16X_EMB_FUNC_FIFO_EN_B, (uint8_t *)&emb_func_fifo_en_b, 1);
  if (ret == 0)
  {
    *val = emb_func_fifo_en_b.mlc_filter_feature_fifo_en;
  }

  ret += lsm6dsv16x_mem_bank_set(ctx, LSM6DSV16X_MAIN_MEM_BANK);

  return ret;
}


int32_t lsm6dsv16x_fifo_sh_batch_slave_set(const stmdev_ctx_t *ctx, uint8_t idx, uint8_t val)
{
  lsm6dsv16x_slv0_config_t slv_config = {0};
  int32_t ret = 0;

  ret = lsm6dsv16x_mem_bank_set(ctx, LSM6DSV16X_SENSOR_HUB_MEM_BANK);
  if (ret != 0)
  {
    return ret;
  }

  ret = lsm6dsv16x_read_reg(ctx, LSM6DSV16X_SLV0_CONFIG + idx * 3U, (uint8_t *)&slv_config, 1);
  if (ret == 0)
  {
    slv_config.batch_ext_sens_0_en = val;
    ret += lsm6dsv16x_write_reg(ctx, LSM6DSV16X_SLV0_CONFIG + idx * 3U, (uint8_t *)&slv_config, 1);
  }

  ret += lsm6dsv16x_mem_bank_set(ctx, LSM6DSV16X_MAIN_MEM_BANK);

  return ret;
}


int32_t lsm6dsv16x_fifo_sh_batch_slave_get(const stmdev_ctx_t *ctx, uint8_t idx, uint8_t *val)
{
  lsm6dsv16x_slv0_config_t slv_config = {0};
  int32_t ret = 0;

  ret = lsm6dsv16x_mem_bank_set(ctx, LSM6DSV16X_SENSOR_HUB_MEM_BANK);
  if (ret != 0)
  {
    return ret;
  }

  ret = lsm6dsv16x_read_reg(ctx, LSM6DSV16X_SLV0_CONFIG + idx * 3U, (uint8_t *)&slv_config, 1);
  if (ret == 0)
  {
    *val = slv_config.batch_ext_sens_0_en;
  }

  ret += lsm6dsv16x_mem_bank_set(ctx, LSM6DSV16X_MAIN_MEM_BANK);

  return ret;
}


int32_t lsm6dsv16x_fifo_sflp_batch_set(const stmdev_ctx_t *ctx,
                                       lsm6dsv16x_fifo_sflp_raw_t val)
{
  lsm6dsv16x_emb_func_fifo_en_a_t emb_func_fifo_en_a = {0};
  int32_t ret = 0;

  ret = lsm6dsv16x_mem_bank_set(ctx, LSM6DSV16X_EMBED_FUNC_MEM_BANK);
  if (ret == 0)
  {
    ret = lsm6dsv16x_read_reg(ctx, LSM6DSV16X_EMB_FUNC_FIFO_EN_A, (uint8_t *)&emb_func_fifo_en_a, 1);
  }
  if (ret == 0)
  {
    emb_func_fifo_en_a.sflp_game_fifo_en = val.game_rotation;
    emb_func_fifo_en_a.sflp_gravity_fifo_en = val.gravity;
    emb_func_fifo_en_a.sflp_gbias_fifo_en = val.gbias;
    ret += lsm6dsv16x_write_reg(ctx, LSM6DSV16X_EMB_FUNC_FIFO_EN_A,
                                (uint8_t *)&emb_func_fifo_en_a, 1);
  }

  ret += lsm6dsv16x_mem_bank_set(ctx, LSM6DSV16X_MAIN_MEM_BANK);

  return ret;
}


int32_t lsm6dsv16x_fifo_sflp_batch_get(const stmdev_ctx_t *ctx,
                                       lsm6dsv16x_fifo_sflp_raw_t *val)
{
  lsm6dsv16x_emb_func_fifo_en_a_t emb_func_fifo_en_a = {0};
  int32_t ret = 0;

  ret = lsm6dsv16x_mem_bank_set(ctx, LSM6DSV16X_EMBED_FUNC_MEM_BANK);
  if (ret == 0)
  {
    ret = lsm6dsv16x_read_reg(ctx, LSM6DSV16X_EMB_FUNC_FIFO_EN_A, (uint8_t *)&emb_func_fifo_en_a, 1);
  }
  if (ret == 0)
  {
    val->game_rotation = emb_func_fifo_en_a.sflp_game_fifo_en;
    val->gravity = emb_func_fifo_en_a.sflp_gravity_fifo_en;
    val->gbias = emb_func_fifo_en_a.sflp_gbias_fifo_en;
  }

  ret += lsm6dsv16x_mem_bank_set(ctx, LSM6DSV16X_MAIN_MEM_BANK);

  return ret;
}

int32_t lsm6dsv16x_filt_anti_spike_set(const stmdev_ctx_t *ctx,
                                       lsm6dsv16x_filt_anti_spike_t val)
{
  lsm6dsv16x_if_cfg_t if_cfg = {0};
  int32_t ret = 0;

  ret = lsm6dsv16x_read_reg(ctx, LSM6DSV16X_IF_CFG, (uint8_t *)&if_cfg, 1);

  if (ret == 0)
  {
    if_cfg.asf_ctrl = (uint8_t)val & 0x01U;
    ret = lsm6dsv16x_write_reg(ctx, LSM6DSV16X_IF_CFG, (uint8_t *)&if_cfg, 1);
  }

  return ret;
}


int32_t lsm6dsv16x_filt_anti_spike_get(const stmdev_ctx_t *ctx,
                                       lsm6dsv16x_filt_anti_spike_t *val)
{
  lsm6dsv16x_if_cfg_t if_cfg = {0};
  int32_t ret = 0;

  ret = lsm6dsv16x_read_reg(ctx, LSM6DSV16X_IF_CFG, (uint8_t *)&if_cfg, 1);
  if (ret != 0)
  {
    return ret;
  }

  switch (if_cfg.asf_ctrl)
  {
    case 0x00:
      *val = LSM6DSV16X_AUTO;
      break;

    case 0x01:
      *val = LSM6DSV16X_ALWAYS_ACTIVE;
      break;

    default:
      *val = LSM6DSV16X_AUTO;
      break;
  }

  return ret;
}


int32_t lsm6dsv16x_filt_settling_mask_set(const stmdev_ctx_t *ctx,
                                          lsm6dsv16x_filt_settling_mask_t val)
{
  lsm6dsv16x_emb_func_cfg_t emb_func_cfg = {0};
  lsm6dsv16x_ui_int_ois_t ui_int_ois = {0};
  lsm6dsv16x_ctrl4_t ctrl4 = {0};
  int32_t ret = 0;

  ret = lsm6dsv16x_read_reg(ctx, LSM6DSV16X_CTRL4, (uint8_t *)&ctrl4, 1);
  if (ret != 0)
  {
    return ret;
  }
  ctrl4.drdy_mask = val.drdy;
  ret += lsm6dsv16x_write_reg(ctx, LSM6DSV16X_CTRL4, (uint8_t *)&ctrl4, 1);
  if (ret != 0)
  {
    return ret;
  }

  ret = lsm6dsv16x_read_reg(ctx, LSM6DSV16X_EMB_FUNC_CFG, (uint8_t *)&emb_func_cfg, 1);
  if (ret != 0)
  {
    return ret;
  }
  emb_func_cfg.emb_func_irq_mask_xl_settl = val.irq_xl;
  emb_func_cfg.emb_func_irq_mask_g_settl = val.irq_g;
  ret += lsm6dsv16x_write_reg(ctx, LSM6DSV16X_EMB_FUNC_CFG, (uint8_t *)&emb_func_cfg, 1);
  if (ret != 0)
  {
    return ret;
  }

  ret = lsm6dsv16x_read_reg(ctx, LSM6DSV16X_UI_INT_OIS, (uint8_t *)&ui_int_ois, 1);
  if (ret != 0)
  {
    return ret;
  }
  ui_int_ois.drdy_mask_ois = val.ois_drdy;
  ret += lsm6dsv16x_write_reg(ctx, LSM6DSV16X_UI_INT_OIS, (uint8_t *)&ui_int_ois, 1);

  return ret;
}


int32_t lsm6dsv16x_filt_settling_mask_get(const stmdev_ctx_t *ctx,
                                          lsm6dsv16x_filt_settling_mask_t *val)
{
  lsm6dsv16x_emb_func_cfg_t emb_func_cfg = {0};
  lsm6dsv16x_ui_int_ois_t ui_int_ois = {0};
  lsm6dsv16x_ctrl4_t ctrl4 = {0};
  int32_t ret = 0;

  ret = lsm6dsv16x_read_reg(ctx, LSM6DSV16X_CTRL4, (uint8_t *)&ctrl4, 1);
  ret += lsm6dsv16x_read_reg(ctx, LSM6DSV16X_EMB_FUNC_CFG, (uint8_t *)&emb_func_cfg, 1);
  ret += lsm6dsv16x_read_reg(ctx, LSM6DSV16X_UI_INT_OIS, (uint8_t *)&ui_int_ois, 1);
  if (ret != 0)
  {
    return ret;
  }

  val->irq_xl = emb_func_cfg.emb_func_irq_mask_xl_settl;
  val->irq_g = emb_func_cfg.emb_func_irq_mask_g_settl;
  val->drdy = ctrl4.drdy_mask;

  return ret;
}


int32_t lsm6dsv16x_filt_ois_settling_mask_set(const stmdev_ctx_t *ctx,
                                              lsm6dsv16x_filt_ois_settling_mask_t val)
{
  lsm6dsv16x_spi2_int_ois_t spi2_int_ois = {0};
  int32_t ret = 0;

  ret = lsm6dsv16x_read_reg(ctx, LSM6DSV16X_SPI2_INT_OIS, (uint8_t *)&spi2_int_ois, 1);

  if (ret == 0)
  {
    spi2_int_ois.drdy_mask_ois = val.ois_drdy;
    ret = lsm6dsv16x_write_reg(ctx, LSM6DSV16X_SPI2_INT_OIS, (uint8_t *)&spi2_int_ois, 1);
  }

  return ret;
}


int32_t lsm6dsv16x_filt_ois_settling_mask_get(const stmdev_ctx_t *ctx,
                                              lsm6dsv16x_filt_ois_settling_mask_t *val)
{

  lsm6dsv16x_spi2_int_ois_t spi2_int_ois = {0};
  int32_t ret = 0;

  ret = lsm6dsv16x_read_reg(ctx, LSM6DSV16X_SPI2_INT_OIS, (uint8_t *)&spi2_int_ois, 1);
  if (ret != 0)
  {
    return ret;
  }

  val->ois_drdy = spi2_int_ois.drdy_mask_ois;

  return ret;
}


int32_t lsm6dsv16x_filt_gy_lp1_bandwidth_set(const stmdev_ctx_t *ctx,
                                             lsm6dsv16x_filt_gy_lp1_bandwidth_t val)
{
  lsm6dsv16x_ctrl6_t ctrl6 = {0};
  int32_t ret = 0;

  ret = lsm6dsv16x_read_reg(ctx, LSM6DSV16X_CTRL6, (uint8_t *)&ctrl6, 1);
  if (ret == 0)
  {
    ctrl6.lpf1_g_bw = (uint8_t)val & 0x0Fu;
    ret = lsm6dsv16x_write_reg(ctx, LSM6DSV16X_CTRL6, (uint8_t *)&ctrl6, 1);
  }

  return ret;
}


int32_t lsm6dsv16x_filt_gy_lp1_bandwidth_get(const stmdev_ctx_t *ctx,
                                             lsm6dsv16x_filt_gy_lp1_bandwidth_t *val)
{
  lsm6dsv16x_ctrl6_t ctrl6 = {0};
  int32_t ret = 0;

  ret = lsm6dsv16x_read_reg(ctx, LSM6DSV16X_CTRL6, (uint8_t *)&ctrl6, 1);
  if (ret != 0)
  {
    return ret;
  }

  switch (ctrl6.lpf1_g_bw)
  {
    case 0x00:
      *val = LSM6DSV16X_GY_ULTRA_LIGHT;
      break;

    case 0x01:
      *val = LSM6DSV16X_GY_VERY_LIGHT;
      break;

    case 0x02:
      *val = LSM6DSV16X_GY_LIGHT;
      break;

    case 0x03:
      *val = LSM6DSV16X_GY_MEDIUM;
      break;

    case 0x04:
      *val = LSM6DSV16X_GY_STRONG;
      break;

    case 0x05:
      *val = LSM6DSV16X_GY_VERY_STRONG;
      break;

    case 0x06:
      *val = LSM6DSV16X_GY_AGGRESSIVE;
      break;

    case 0x07:
      *val = LSM6DSV16X_GY_XTREME;
      break;

    default:
      *val = LSM6DSV16X_GY_ULTRA_LIGHT;
      break;
  }

  return ret;
}


int32_t lsm6dsv16x_filt_gy_lp1_set(const stmdev_ctx_t *ctx, uint8_t val)
{
  lsm6dsv16x_ctrl7_t ctrl7 = {0};
  int32_t ret = 0;

  ret = lsm6dsv16x_read_reg(ctx, LSM6DSV16X_CTRL7, (uint8_t *)&ctrl7, 1);
  if (ret == 0)
  {
    ctrl7.lpf1_g_en = val;
    ret = lsm6dsv16x_write_reg(ctx, LSM6DSV16X_CTRL7, (uint8_t *)&ctrl7, 1);
  }

  return ret;
}


int32_t lsm6dsv16x_filt_gy_lp1_get(const stmdev_ctx_t *ctx, uint8_t *val)
{
  lsm6dsv16x_ctrl7_t ctrl7 = {0};
  int32_t ret = 0;

  ret = lsm6dsv16x_read_reg(ctx, LSM6DSV16X_CTRL7, (uint8_t *)&ctrl7, 1);
  if (ret != 0)
  {
    return ret;
  }

  *val = ctrl7.lpf1_g_en;

  return ret;
}


int32_t lsm6dsv16x_filt_xl_lp2_bandwidth_set(const stmdev_ctx_t *ctx,
                                             lsm6dsv16x_filt_xl_lp2_bandwidth_t val)
{
  lsm6dsv16x_ctrl8_t ctrl8 = {0};
  int32_t ret = 0;

  ret = lsm6dsv16x_read_reg(ctx, LSM6DSV16X_CTRL8, (uint8_t *)&ctrl8, 1);
  if (ret == 0)
  {
    ctrl8.hp_lpf2_xl_bw = (uint8_t)val & 0x07U;
    ret = lsm6dsv16x_write_reg(ctx, LSM6DSV16X_CTRL8, (uint8_t *)&ctrl8, 1);
  }

  return ret;
}


int32_t lsm6dsv16x_filt_xl_lp2_bandwidth_get(const stmdev_ctx_t *ctx,
                                             lsm6dsv16x_filt_xl_lp2_bandwidth_t *val)
{
  lsm6dsv16x_ctrl8_t ctrl8 = {0};
  int32_t ret = 0;

  ret = lsm6dsv16x_read_reg(ctx, LSM6DSV16X_CTRL8, (uint8_t *)&ctrl8, 1);
  if (ret != 0)
  {
    return ret;
  }

  switch (ctrl8.hp_lpf2_xl_bw)
  {
    case 0x00:
      *val = LSM6DSV16X_XL_ULTRA_LIGHT;
      break;

    case 0x01:
      *val = LSM6DSV16X_XL_VERY_LIGHT;
      break;

    case 0x02:
      *val = LSM6DSV16X_XL_LIGHT;
      break;

    case 0x03:
      *val = LSM6DSV16X_XL_MEDIUM;
      break;

    case 0x04:
      *val = LSM6DSV16X_XL_STRONG;
      break;

    case 0x05:
      *val = LSM6DSV16X_XL_VERY_STRONG;
      break;

    case 0x06:
      *val = LSM6DSV16X_XL_AGGRESSIVE;
      break;

    case 0x07:
      *val = LSM6DSV16X_XL_XTREME;
      break;

    default:
      *val = LSM6DSV16X_XL_ULTRA_LIGHT;
      break;
  }

  return ret;
}


int32_t lsm6dsv16x_filt_xl_lp2_set(const stmdev_ctx_t *ctx, uint8_t val)
{
  lsm6dsv16x_ctrl9_t ctrl9 = {0};
  int32_t ret = 0;

  ret = lsm6dsv16x_read_reg(ctx, LSM6DSV16X_CTRL9, (uint8_t *)&ctrl9, 1);
  if (ret == 0)
  {
    ctrl9.lpf2_xl_en = val;
    ret = lsm6dsv16x_write_reg(ctx, LSM6DSV16X_CTRL9, (uint8_t *)&ctrl9, 1);
  }

  return ret;
}


int32_t lsm6dsv16x_filt_xl_lp2_get(const stmdev_ctx_t *ctx, uint8_t *val)
{
  lsm6dsv16x_ctrl9_t ctrl9 = {0};
  int32_t ret = 0;

  ret = lsm6dsv16x_read_reg(ctx, LSM6DSV16X_CTRL9, (uint8_t *)&ctrl9, 1);
  if (ret != 0)
  {
    return ret;
  }

  *val = ctrl9.lpf2_xl_en;

  return ret;
}

int32_t lsm6dsv16x_filt_xl_hp_set(const stmdev_ctx_t *ctx, uint8_t val)
{
  lsm6dsv16x_ctrl9_t ctrl9 = {0};
  int32_t ret = 0;

  ret = lsm6dsv16x_read_reg(ctx, LSM6DSV16X_CTRL9, (uint8_t *)&ctrl9, 1);
  if (ret == 0)
  {
    ctrl9.hp_slope_xl_en = val;
    ret = lsm6dsv16x_write_reg(ctx, LSM6DSV16X_CTRL9, (uint8_t *)&ctrl9, 1);
  }

  return ret;
}


int32_t lsm6dsv16x_filt_xl_hp_get(const stmdev_ctx_t *ctx, uint8_t *val)
{
  lsm6dsv16x_ctrl9_t ctrl9 = {0};
  int32_t ret = 0;

  ret = lsm6dsv16x_read_reg(ctx, LSM6DSV16X_CTRL9, (uint8_t *)&ctrl9, 1);
  if (ret != 0)
  {
    return ret;
  }

  *val = ctrl9.hp_slope_xl_en;

  return ret;
}

int32_t lsm6dsv16x_filt_xl_fast_settling_set(const stmdev_ctx_t *ctx, uint8_t val)
{
  lsm6dsv16x_ctrl9_t ctrl9 = {0};
  int32_t ret = 0;

  ret = lsm6dsv16x_read_reg(ctx, LSM6DSV16X_CTRL9, (uint8_t *)&ctrl9, 1);
  if (ret == 0)
  {
    ctrl9.xl_fastsettl_mode = val;
    ret = lsm6dsv16x_write_reg(ctx, LSM6DSV16X_CTRL9, (uint8_t *)&ctrl9, 1);
  }

  return ret;
}


int32_t lsm6dsv16x_filt_xl_fast_settling_get(const stmdev_ctx_t *ctx, uint8_t *val)
{
  lsm6dsv16x_ctrl9_t ctrl9 = {0};
  int32_t ret = 0;

  ret = lsm6dsv16x_read_reg(ctx, LSM6DSV16X_CTRL9, (uint8_t *)&ctrl9, 1);
  if (ret != 0)
  {
    return ret;
  }

  *val = ctrl9.xl_fastsettl_mode;

  return ret;
}

int32_t lsm6dsv16x_filt_xl_hp_mode_set(const stmdev_ctx_t *ctx,
                                       lsm6dsv16x_filt_xl_hp_mode_t val)
{
  lsm6dsv16x_ctrl9_t ctrl9 = {0};
  int32_t ret = 0;

  ret = lsm6dsv16x_read_reg(ctx, LSM6DSV16X_CTRL9, (uint8_t *)&ctrl9, 1);
  if (ret == 0)
  {
    ctrl9.hp_ref_mode_xl = (uint8_t)val & 0x01U;
    ret = lsm6dsv16x_write_reg(ctx, LSM6DSV16X_CTRL9, (uint8_t *)&ctrl9, 1);
  }

  return ret;
}


int32_t lsm6dsv16x_filt_xl_hp_mode_get(const stmdev_ctx_t *ctx,
                                       lsm6dsv16x_filt_xl_hp_mode_t *val)
{
  lsm6dsv16x_ctrl9_t ctrl9 = {0};
  int32_t ret = 0;

  ret = lsm6dsv16x_read_reg(ctx, LSM6DSV16X_CTRL9, (uint8_t *)&ctrl9, 1);
  if (ret != 0)
  {
    return ret;
  }

  switch (ctrl9.hp_ref_mode_xl)
  {
    case 0x00:
      *val = LSM6DSV16X_HP_MD_NORMAL;
      break;

    case 0x01:
      *val = LSM6DSV16X_HP_MD_REFERENCE;
      break;

    default:
      *val = LSM6DSV16X_HP_MD_NORMAL;
      break;
  }

  return ret;
}


int32_t lsm6dsv16x_filt_wkup_act_feed_set(const stmdev_ctx_t *ctx,
                                          lsm6dsv16x_filt_wkup_act_feed_t val)
{
  lsm6dsv16x_wake_up_ths_t wake_up_ths = {0};
  lsm6dsv16x_tap_cfg0_t tap_cfg0 = {0};
  int32_t ret = 0;

  ret = lsm6dsv16x_read_reg(ctx, LSM6DSV16X_WAKE_UP_THS, (uint8_t *)&wake_up_ths, 1);
  ret += lsm6dsv16x_read_reg(ctx, LSM6DSV16X_TAP_CFG0, (uint8_t *)&tap_cfg0, 1);
  if (ret != 0)
  {
    return ret;
  }

  tap_cfg0.slope_fds = (uint8_t)val & 0x01U;
  ret = lsm6dsv16x_write_reg(ctx, LSM6DSV16X_TAP_CFG0, (uint8_t *)&tap_cfg0, 1);
  if (ret != 0)
  {
    return ret;
  }

  wake_up_ths.usr_off_on_wu = ((uint8_t)val & 0x02U) >> 1;
  ret = lsm6dsv16x_write_reg(ctx, LSM6DSV16X_WAKE_UP_THS, (uint8_t *)&wake_up_ths, 1);

  return ret;
}


int32_t lsm6dsv16x_filt_wkup_act_feed_get(const stmdev_ctx_t *ctx,
                                          lsm6dsv16x_filt_wkup_act_feed_t *val)
{
  lsm6dsv16x_wake_up_ths_t wake_up_ths = {0};
  lsm6dsv16x_tap_cfg0_t tap_cfg0 = {0};
  int32_t ret = 0;

  ret = lsm6dsv16x_read_reg(ctx, LSM6DSV16X_WAKE_UP_THS, (uint8_t *)&wake_up_ths, 1);
  ret += lsm6dsv16x_read_reg(ctx, LSM6DSV16X_TAP_CFG0, (uint8_t *)&tap_cfg0, 1);
  if (ret != 0)
  {
    return ret;
  }

  switch ((wake_up_ths.usr_off_on_wu << 1) + tap_cfg0.slope_fds)
  {
    case 0x00:
      *val = LSM6DSV16X_WK_FEED_SLOPE;
      break;

    case 0x01:
      *val = LSM6DSV16X_WK_FEED_HIGH_PASS;
      break;

    case 0x02:
      *val = LSM6DSV16X_WK_FEED_LP_WITH_OFFSET;
      break;

    default:
      *val = LSM6DSV16X_WK_FEED_SLOPE;
      break;
  }

  return ret;
}


int32_t lsm6dsv16x_mask_trigger_xl_settl_set(const stmdev_ctx_t *ctx, uint8_t val)
{
  lsm6dsv16x_tap_cfg0_t tap_cfg0 = {0};
  int32_t ret = 0;

  ret = lsm6dsv16x_read_reg(ctx, LSM6DSV16X_TAP_CFG0, (uint8_t *)&tap_cfg0, 1);

  if (ret == 0)
  {
    tap_cfg0.hw_func_mask_xl_settl = val & 0x01U;
    ret = lsm6dsv16x_write_reg(ctx, LSM6DSV16X_TAP_CFG0, (uint8_t *)&tap_cfg0, 1);
  }

  return ret;
}


int32_t lsm6dsv16x_mask_trigger_xl_settl_get(const stmdev_ctx_t *ctx, uint8_t *val)
{
  lsm6dsv16x_tap_cfg0_t tap_cfg0 = {0};
  int32_t ret = 0;

  ret = lsm6dsv16x_read_reg(ctx, LSM6DSV16X_TAP_CFG0, (uint8_t *)&tap_cfg0, 1);
  if (ret != 0)
  {
    return ret;
  }

  *val = tap_cfg0.hw_func_mask_xl_settl;

  return ret;
}


int32_t lsm6dsv16x_filt_sixd_feed_set(const stmdev_ctx_t *ctx,
                                      lsm6dsv16x_filt_sixd_feed_t val)
{
  lsm6dsv16x_tap_cfg0_t tap_cfg0 = {0};
  int32_t ret = 0;

  ret = lsm6dsv16x_read_reg(ctx, LSM6DSV16X_TAP_CFG0, (uint8_t *)&tap_cfg0, 1);

  if (ret == 0)
  {
    tap_cfg0.low_pass_on_6d = (uint8_t)val & 0x01U;
    ret = lsm6dsv16x_write_reg(ctx, LSM6DSV16X_TAP_CFG0, (uint8_t *)&tap_cfg0, 1);
  }

  return ret;
}


int32_t lsm6dsv16x_filt_sixd_feed_get(const stmdev_ctx_t *ctx,
                                      lsm6dsv16x_filt_sixd_feed_t *val)
{
  lsm6dsv16x_tap_cfg0_t tap_cfg0 = {0};
  int32_t ret = 0;

  ret = lsm6dsv16x_read_reg(ctx, LSM6DSV16X_TAP_CFG0, (uint8_t *)&tap_cfg0, 1);
  if (ret != 0)
  {
    return ret;
  }

  switch (tap_cfg0.low_pass_on_6d)
  {
    case 0x00:
      *val = LSM6DSV16X_SIXD_FEED_ODR_DIV_2;
      break;

    case 0x01:
      *val = LSM6DSV16X_SIXD_FEED_LOW_PASS;
      break;

    default:
      *val = LSM6DSV16X_SIXD_FEED_ODR_DIV_2;
      break;
  }

  return ret;
}


int32_t lsm6dsv16x_filt_gy_eis_lp_bandwidth_set(const stmdev_ctx_t *ctx,
                                                lsm6dsv16x_filt_gy_eis_lp_bandwidth_t val)
{
  lsm6dsv16x_ctrl_eis_t ctrl_eis = {0};
  int32_t ret = 0;

  ret = lsm6dsv16x_read_reg(ctx, LSM6DSV16X_CTRL_EIS, (uint8_t *)&ctrl_eis, 1);

  if (ret == 0)
  {
    ctrl_eis.lpf_g_eis_bw = (uint8_t)val & 0x01U;
    ret = lsm6dsv16x_write_reg(ctx, LSM6DSV16X_CTRL_EIS, (uint8_t *)&ctrl_eis, 1);
  }

  return ret;
}


int32_t lsm6dsv16x_filt_gy_eis_lp_bandwidth_get(const stmdev_ctx_t *ctx,
                                                lsm6dsv16x_filt_gy_eis_lp_bandwidth_t *val)
{
  lsm6dsv16x_ctrl_eis_t ctrl_eis = {0};
  int32_t ret = 0;

  ret = lsm6dsv16x_read_reg(ctx, LSM6DSV16X_CTRL_EIS, (uint8_t *)&ctrl_eis, 1);
  if (ret != 0)
  {
    return ret;
  }

  switch (ctrl_eis.lpf_g_eis_bw)
  {
    case 0x00:
      *val = LSM6DSV16X_EIS_LP_NORMAL;
      break;

    case 0x01:
      *val = LSM6DSV16X_EIS_LP_LIGHT;
      break;

    default:
      *val = LSM6DSV16X_EIS_LP_NORMAL;
      break;
  }

  return ret;
}


int32_t lsm6dsv16x_filt_gy_ois_lp_bandwidth_set(const stmdev_ctx_t *ctx,
                                                lsm6dsv16x_filt_gy_ois_lp_bandwidth_t val)
{
  lsm6dsv16x_ui_ctrl2_ois_t ui_ctrl2_ois = {0};
  int32_t ret = 0;

  ret = lsm6dsv16x_read_reg(ctx, LSM6DSV16X_UI_CTRL2_OIS, (uint8_t *)&ui_ctrl2_ois, 1);

  if (ret == 0)
  {
    ui_ctrl2_ois.lpf1_g_ois_bw = (uint8_t)val & 0x03U;
    ret = lsm6dsv16x_write_reg(ctx, LSM6DSV16X_UI_CTRL2_OIS, (uint8_t *)&ui_ctrl2_ois, 1);
  }

  return ret;
}


int32_t lsm6dsv16x_filt_gy_ois_lp_bandwidth_get(const stmdev_ctx_t *ctx,
                                                lsm6dsv16x_filt_gy_ois_lp_bandwidth_t *val)
{

  lsm6dsv16x_ui_ctrl2_ois_t ui_ctrl2_ois = {0};
  int32_t ret = 0;

  ret = lsm6dsv16x_read_reg(ctx, LSM6DSV16X_UI_CTRL2_OIS, (uint8_t *)&ui_ctrl2_ois, 1);
  if (ret != 0)
  {
    return ret;
  }

  switch (ui_ctrl2_ois.lpf1_g_ois_bw)
  {
    case 0x00:
      *val = LSM6DSV16X_OIS_GY_LP_NORMAL;
      break;

    case 0x01:
      *val = LSM6DSV16X_OIS_GY_LP_STRONG;
      break;

    case 0x02:
      *val = LSM6DSV16X_OIS_GY_LP_AGGRESSIVE;
      break;

    case 0x03:
      *val = LSM6DSV16X_OIS_GY_LP_LIGHT;
      break;

    default:
      *val = LSM6DSV16X_OIS_GY_LP_NORMAL;
      break;
  }

  return ret;
}


int32_t lsm6dsv16x_filt_xl_ois_lp_bandwidth_set(const stmdev_ctx_t *ctx,
                                                lsm6dsv16x_filt_xl_ois_lp_bandwidth_t val)
{
  lsm6dsv16x_ui_ctrl3_ois_t ui_ctrl3_ois = {0};
  int32_t ret = 0;

  ret = lsm6dsv16x_read_reg(ctx, LSM6DSV16X_UI_CTRL3_OIS, (uint8_t *)&ui_ctrl3_ois, 1);

  if (ret == 0)
  {
    ui_ctrl3_ois.lpf_xl_ois_bw = (uint8_t)val & 0x07U;
    ret = lsm6dsv16x_write_reg(ctx, LSM6DSV16X_UI_CTRL3_OIS, (uint8_t *)&ui_ctrl3_ois, 1);
  }

  return ret;
}


int32_t lsm6dsv16x_filt_xl_ois_lp_bandwidth_get(const stmdev_ctx_t *ctx,
                                                lsm6dsv16x_filt_xl_ois_lp_bandwidth_t *val)
{
  lsm6dsv16x_ui_ctrl3_ois_t ui_ctrl3_ois = {0};
  int32_t ret = 0;

  ret = lsm6dsv16x_read_reg(ctx, LSM6DSV16X_UI_CTRL3_OIS, (uint8_t *)&ui_ctrl3_ois, 1);
  if (ret != 0)
  {
    return ret;
  }

  switch (ui_ctrl3_ois.lpf_xl_ois_bw)
  {
    case 0x00:
      *val = LSM6DSV16X_OIS_XL_LP_ULTRA_LIGHT;
      break;

    case 0x01:
      *val = LSM6DSV16X_OIS_XL_LP_VERY_LIGHT;
      break;

    case 0x02:
      *val = LSM6DSV16X_OIS_XL_LP_LIGHT;
      break;

    case 0x03:
      *val = LSM6DSV16X_OIS_XL_LP_NORMAL;
      break;

    case 0x04:
      *val = LSM6DSV16X_OIS_XL_LP_STRONG;
      break;

    case 0x05:
      *val = LSM6DSV16X_OIS_XL_LP_VERY_STRONG;
      break;

    case 0x06:
      *val = LSM6DSV16X_OIS_XL_LP_AGGRESSIVE;
      break;

    case 0x07:
      *val = LSM6DSV16X_OIS_XL_LP_XTREME;
      break;

    default:
      *val = LSM6DSV16X_OIS_XL_LP_ULTRA_LIGHT;
      break;
  }

  return ret;
}

int32_t lsm6dsv16x_fsm_permission_set(const stmdev_ctx_t *ctx,
                                      lsm6dsv16x_fsm_permission_t val)
{
  lsm6dsv16x_func_cfg_access_t func_cfg_access = {0};
  int32_t ret = 0;

  ret = lsm6dsv16x_read_reg(ctx, LSM6DSV16X_FUNC_CFG_ACCESS, (uint8_t *)&func_cfg_access, 1);

  if (ret == 0)
  {
    func_cfg_access.fsm_wr_ctrl_en = (uint8_t)val & 0x01U;
    ret = lsm6dsv16x_write_reg(ctx, LSM6DSV16X_FUNC_CFG_ACCESS, (uint8_t *)&func_cfg_access, 1);
  }

  return ret;
}


int32_t lsm6dsv16x_fsm_permission_get(const stmdev_ctx_t *ctx,
                                      lsm6dsv16x_fsm_permission_t *val)
{
  lsm6dsv16x_func_cfg_access_t func_cfg_access = {0};
  int32_t ret = 0;

  ret = lsm6dsv16x_read_reg(ctx, LSM6DSV16X_FUNC_CFG_ACCESS, (uint8_t *)&func_cfg_access, 1);
  if (ret != 0)
  {
    return ret;
  }

  switch (func_cfg_access.fsm_wr_ctrl_en)
  {
    case 0x00:
      *val = LSM6DSV16X_PROTECT_CTRL_REGS;
      break;

    case 0x01:
      *val = LSM6DSV16X_WRITE_CTRL_REG;
      break;

    default:
      *val = LSM6DSV16X_PROTECT_CTRL_REGS;
      break;
  }

  return ret;
}


int32_t lsm6dsv16x_fsm_permission_status(const stmdev_ctx_t *ctx, uint8_t *val)
{
  lsm6dsv16x_ctrl_status_t ctrl_status = {0};
  int32_t ret = 0;

  ret = lsm6dsv16x_read_reg(ctx, LSM6DSV16X_CTRL_STATUS, (uint8_t *)&ctrl_status, 1);
  if (ret != 0)
  {
    return ret;
  }

  *val = ctrl_status.fsm_wr_ctrl_status;

  return ret;
}


int32_t lsm6dsv16x_fsm_mode_set(const stmdev_ctx_t *ctx, lsm6dsv16x_fsm_mode_t val)
{
  lsm6dsv16x_emb_func_en_b_t emb_func_en_b = {0};
  lsm6dsv16x_fsm_enable_t fsm_enable = {0};
  int32_t ret = 0;

  ret = lsm6dsv16x_mem_bank_set(ctx, LSM6DSV16X_EMBED_FUNC_MEM_BANK);
  if (ret != 0)
  {
    return ret;
  }

  ret = lsm6dsv16x_read_reg(ctx, LSM6DSV16X_EMB_FUNC_EN_B, (uint8_t *)&emb_func_en_b, 1);
  ret += lsm6dsv16x_read_reg(ctx, LSM6DSV16X_FSM_ENABLE, (uint8_t *)&fsm_enable, 1);
  if (ret != 0)
  {
    goto exit;
  }

  if ((val.fsm1_en | val.fsm2_en | val.fsm3_en | val.fsm4_en
       | val.fsm5_en | val.fsm6_en | val.fsm7_en | val.fsm8_en) == PROPERTY_ENABLE)
  {
    emb_func_en_b.fsm_en = PROPERTY_ENABLE;
  }
  else
  {
    emb_func_en_b.fsm_en = PROPERTY_DISABLE;
  }

  fsm_enable.fsm1_en = val.fsm1_en;
  fsm_enable.fsm2_en = val.fsm2_en;
  fsm_enable.fsm3_en = val.fsm3_en;
  fsm_enable.fsm4_en = val.fsm4_en;
  fsm_enable.fsm5_en = val.fsm5_en;
  fsm_enable.fsm6_en = val.fsm6_en;
  fsm_enable.fsm7_en = val.fsm7_en;
  fsm_enable.fsm8_en = val.fsm8_en;

  ret = lsm6dsv16x_write_reg(ctx, LSM6DSV16X_FSM_ENABLE, (uint8_t *)&fsm_enable, 1);
  ret += lsm6dsv16x_write_reg(ctx, LSM6DSV16X_EMB_FUNC_EN_B, (uint8_t *)&emb_func_en_b, 1);

exit:
  ret += lsm6dsv16x_mem_bank_set(ctx, LSM6DSV16X_MAIN_MEM_BANK);

  return ret;
}


int32_t lsm6dsv16x_fsm_mode_get(const stmdev_ctx_t *ctx, lsm6dsv16x_fsm_mode_t *val)
{
  lsm6dsv16x_fsm_enable_t fsm_enable = {0};
  int32_t ret = 0;

  ret = lsm6dsv16x_mem_bank_set(ctx, LSM6DSV16X_EMBED_FUNC_MEM_BANK);
  if (ret != 0)
  {
    return ret;
  }
  ret += lsm6dsv16x_read_reg(ctx, LSM6DSV16X_FSM_ENABLE, (uint8_t *)&fsm_enable, 1);
  ret += lsm6dsv16x_mem_bank_set(ctx, LSM6DSV16X_MAIN_MEM_BANK);
  if (ret != 0)
  {
    return ret;
  }

  val->fsm1_en = fsm_enable.fsm1_en;
  val->fsm2_en = fsm_enable.fsm2_en;
  val->fsm3_en = fsm_enable.fsm3_en;
  val->fsm4_en = fsm_enable.fsm4_en;
  val->fsm5_en = fsm_enable.fsm5_en;
  val->fsm6_en = fsm_enable.fsm6_en;
  val->fsm7_en = fsm_enable.fsm7_en;
  val->fsm8_en = fsm_enable.fsm8_en;

  return ret;
}


int32_t lsm6dsv16x_fsm_long_cnt_set(const stmdev_ctx_t *ctx, uint16_t val)
{
  uint8_t buff[2] = {0};
  int32_t ret = 0;

  buff[1] = (uint8_t)(val / 256U);
  buff[0] = (uint8_t)(val - (buff[1] * 256U));

  ret = lsm6dsv16x_mem_bank_set(ctx, LSM6DSV16X_EMBED_FUNC_MEM_BANK);
  if (ret != 0)
  {
    return ret;
  }
  ret += lsm6dsv16x_write_reg(ctx, LSM6DSV16X_FSM_LONG_COUNTER_L, (uint8_t *)&buff[0], 2);
  ret += lsm6dsv16x_mem_bank_set(ctx, LSM6DSV16X_MAIN_MEM_BANK);

  return ret;
}


int32_t lsm6dsv16x_fsm_long_cnt_get(const stmdev_ctx_t *ctx, uint16_t *val)
{
  uint8_t buff[2] = {0};
  int32_t ret = 0;

  ret = lsm6dsv16x_mem_bank_set(ctx, LSM6DSV16X_EMBED_FUNC_MEM_BANK);
  if (ret != 0)
  {
    return ret;
  }
  ret += lsm6dsv16x_read_reg(ctx, LSM6DSV16X_FSM_LONG_COUNTER_L, &buff[0], 2);
  ret += lsm6dsv16x_mem_bank_set(ctx, LSM6DSV16X_MAIN_MEM_BANK);
  if (ret != 0)
  {
    return ret;
  }

  *val = buff[1];
  *val = (*val * 256U) + buff[0];

  return ret;
}
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
